jackwayne234/binary-optical-chip/Research/papers/paper_source/main.tex

\documentclass{article}
\usepackage{graphicx} % Required for inserting images

\title{Wavelength Ternary Computing}
\author{Christopher Jack Wayne Riner}
\date{January 2026}

\begin{document}

\maketitle

\section{Introduction}

\end{document}
