jackwayne234/binary-optical-chip/docs/SESSION_NOTES_2026-02-02.md

# Session Notes - February 2, 2026

## Summary

Comprehensive session covering GDS chip generation, GitHub organization, and foundry submission preparation for the 81-trit ternary optical computer.

---

## What We Accomplished

### 1. GitHub Repository Cleanup
- Uploaded `ternary_81trit_optimal.gds` to GitHub
- Reorganized root directory:
  - Moved setup guides to `docs/guides/`
  - Moved shell scripts to `bin/`
  - Moved `citations.bib` to `Research/papers/`
- Added `.gitignore` entries for local files (ebay files, CLAUDE.md, etc.)
- Fixed `tools/README.md` URL (Replit → Render.com)
- Updated README with:
  - Table of contents
  - Recent activity section (collapsible)

### 2. Foundry Submission Documents
- Created `Phase3_Chip_Simulation/DESIGN_SUMMARY.md` - complete design datasheet
- Created `Phase3_Chip_Simulation/foundry_inquiry_email.txt` - template email

**Foundries to contact:**
- Applied Nanotools (Canada) - info@appliednt.com
- Ligentec (Switzerland) - mpw@ligentec.com
- HyperLight (Boston) - info@hyperlightcorp.com (best for LiNbO3)
- AIM Photonics (US) - info@aimphotonics.com

### 3. Chip Generator Enhancements

**New components added:**
- `kerr_resonator()` - Optical clock/timing (layer 5)
- `y_junction()` - Beam splitter
- `awg_demux()` - Arrayed Waveguide Grating for R/G/B separation (layer 6)
- `optical_frontend()` - Complete input stage
- `ternary_output_stage()` - 3-channel wavelength-discriminating detector
- `generate_complete_alu()` - Full ALU with frontend + output
- `generate_complete_81_trit()` - Full 81-trit chip

**Menu options:**
```
1-4:  Basic operations (add/sub/mul/div)
5:    Single ALU (configurable)
6:    N-trit processor
7:    Power-of-3 processor
8:    81-trit processor (basic)
9:    Custom components (a-k)
10:   Complete ALU (frontend + ALU + output)
11:   FULL 81-TRIT CHIP [RECOMMENDED]
```

**Labels:**
- Now on dedicated layer **100/0** (toggle in KLayout)
- Shortened to standard naming: SEL_1550, DET_R, A, B, Q, MIX, etc.

### 4. Architecture Clarification

**Signal flow:**
```
CW Laser → Kerr Clock → Y-Junction → AWG (demux) → Selectors → Combiner →
                                                                    ↓
                                                              SFG Mixer
                                                                    ↓
                                                           Splitter → 3 Photodetectors
                                                                    ↓
                                                           DET_R, DET_G, DET_B (to GPIO)
```

**Interface to binary computer:**
- 6 GPIO outputs: V_red_A, V_grn_A, V_blu_A, V_red_B, V_grn_B, V_blu_B
- 3 GPIO inputs: Detect_R, Detect_G, Detect_B
- RGB lasers always on; resonators gate which colors pass
- Computer sets voltages, physics does the math, read output colors

### 5. GDS Files Generated

| File | Description |
|---|---|
| `ternary_81trit_optimal.gds` | Basic 81-trit (option 8) |
| `ternary_complete_alu.gds` | Single complete ALU (option 10) |
| `ternary_81trit_full.gds` | Full 81-trit with frontend (option 11) |
| `optical_frontend.gds` | Frontend only (option 9→k) |

### 6. KLayout Integration
- Created toggle labels macro: `~/.klayout/macros/toggle_labels.lym`
- Keyboard shortcut: **L** (or Tools → Toggle GDS Labels)
- Labels on layer 100/0 for easy visibility toggle

---

## GDS Layers

| Layer | Purpose |
|---|---|
| 1/0 | Waveguide core |
| 2/0 | SFG mixer region (χ²) |
| 3/0 | Photodetector region |
| 4/0 | DFG divider region |
| 5/0 | Kerr nonlinear region |
| 6/0 | AWG body |
| 100/0 | Labels (toggle in KLayout) |

---

## Next Steps

1. **Generate final GDS** - Run option 11 for full 81-trit chip
2. **Convert design summary to PDF**
3. **Send inquiry emails** to foundries
4. **Wait for PDK** from chosen foundry
5. **Regenerate GDS** with foundry-specific layers
6. **Submit for MPW run**

---

## Commands Reference

```bash
# Run chip generator
./launch_chip_generator.sh

# Or manually:
cd /home/jackwayne/Desktop/Optical_computing
source bin/activate_env.sh
python3 Research/programs/ternary_chip_generator.py

# Open GDS in KLayout
klayout Research/data/ternary_81trit_full.gds
```

---

*Session with Claude Code - Opus 4.5*
