jackwayne234/binary-optical-chip/Research/papers/total submission files/updated_paper.tex

\documentclass[journal]{IEEEtran}

% Packages
\usepackage{graphicx}
\usepackage{amsmath}
\usepackage{cite}
\usepackage{url}
\usepackage{hyperref}
\usepackage{float}
\usepackage{booktabs} % For better tables

% Correct hyphenation
\hyphenation{op-tical net-works semi-conduc-tor}

\begin{document}

\title{Wavelength-Division Ternary Logic: Bypassing the Radix Economy Penalty in Optical Computing}

\author{Christopher Riner%
\thanks{Independent Researcher: Chesapeake, VA, US. Email: chrisriner45@gmail.com}}

\maketitle

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

\begin{IEEEkeywords}
Ternary computing, optical computing, wavelength division, radix economy, photonic logic, multi-valued logic
\end{IEEEkeywords}

\section{Introduction}

\subsection{The Ternary Computing Paradox}

Ternary (base-3) computing systems have been recognized since the 1950s as mathematically superior to binary systems. The optimal radix for representing information with minimal hardware cost is Euler's number $e \approx 2.718$, and base-3 is the closest integer radix to this optimum \cite{knuth1981, hayes2001}. Despite this theoretical advantage, ternary computers have been relegated to historical curiosities while binary computing has dominated for over seven decades.

The reason for this paradox is straightforward: with transistor-based digital electronics, implementing a stable three-state element (trit) requires approximately 40 transistors, compared to just 1 transistor for a binary bit \cite{hurst1984}. This 40$\times$ hardware overhead completely eliminates any theoretical advantage from ternary's superior information density. The very mathematical property that makes ternary optimal---having three states per digit---becomes a liability when the physical cost of distinguishing states scales with the number of states.

\subsection{The Promise of Optical Computing}

Photonic computing has emerged as a potential paradigm shift for information processing, offering advantages in speed (light propagates faster than electrons), parallelism (wavelength division multiplexing), and power efficiency (reduced heat dissipation) \cite{miller2010, caulfield2010}. While most optical computing research focuses on binary logic operations, photons possess natural properties that can encode multiple states without the hardware penalties of transistor-based systems:

\begin{itemize}
\item \textbf{Polarization}: Multiple orientations (linear, circular)
\item \textbf{Wavelength}: Discrete frequency channels
\item \textbf{Intensity}: Amplitude levels
\item \textbf{Phase}: Wave timing offsets
\end{itemize}

Existing research in optical ternary computing has primarily exploited polarization states \cite{jin2003, jin2005} or intensity levels \cite{eichmann1986} to encode ternary values. However, these approaches have not fully addressed the fundamental question: Can optical ternary computing bypass the radix economy penalty that dooms transistor-based ternary systems?

\subsection{Our Contribution}

We propose a novel architecture for ternary optical computing based on \textbf{wavelength-selection encoding with external wavelength sources}. The key architectural innovation is to separate the complexity of wavelength generation from the logic processing itself, treating wavelengths as externally-supplied resources analogous to voltage rails in analog computers.

Our specific contributions are:

\begin{enumerate}
\item \textbf{Novel encoding scheme}: Use wavelength selection (choosing ONE of N wavelengths) rather than wavelength-division multiplexing (using N wavelengths simultaneously) or polarization states
\item \textbf{External source architecture}: Generate wavelengths outside the computing fabric, with internal components performing only wavelength-selective routing and switching
\item \textbf{Theoretical analysis}: Show that wavelength-based differentiation has constant cost independent of radix, fundamentally bypassing the traditional radix economy penalty
\item \textbf{Comparison framework}: Contrast with existing polarization-based and intensity-based optical ternary approaches
\end{enumerate}

We demonstrate that this architecture could, in principle, unlock the full 1.58$\times$ information density advantage of ternary logic while avoiding the hardware penalties that have historically prevented ternary computing from practical realization.

\section{Background}

\subsection{Radix Economy and the Optimality of Base-3}

The concept of radix economy addresses the question: What number base minimizes the total hardware cost for representing numbers? This was formalized mathematically by considering two competing factors:

\begin{enumerate}
\item \textbf{Higher radix}: Fewer digits needed to represent a number (proportional to $\log_r(N)$)
\item \textbf{Higher radix}: More complex hardware per digit (proportional to $r$)
\end{enumerate}

The total cost can be expressed as:
\begin{equation}
\text{Cost}(r) = r \times \log_r(N)
\end{equation}

Converting to natural logarithm:
\begin{equation}
\text{Cost}(r) = r \times \frac{\ln(N)}{\ln(r)}
\end{equation}

To minimize, we take the derivative with respect to $r$ and set to zero:
\begin{equation}
\frac{d}{dr}\left[\frac{r}{\ln(r)}\right] = \frac{\ln(r) - 1}{[\ln(r)]^2} = 0
\end{equation}

Solving: $\ln(r) = 1$, therefore $r = e \approx 2.718$.

This proves mathematically that the optimal radix is Euler's number $e$ \cite{hayes2001}. Since we cannot build a base-2.718 computer, we evaluate integer radices:

\begin{itemize}
\item Base-2: Cost = 2.885
\item \textbf{Base-3: Cost = 2.730} (closest to optimal!)
\item Base-4: Cost = 4.000
\item Base-5: Cost = 4.308
\end{itemize}

Base-3 provides approximately \textbf{5.4\% better hardware economy} than binary. Additionally, each ternary digit (trit) carries:
\begin{equation}
\text{Information per trit} = \log_2(3) \approx 1.585 \text{ bits}
\end{equation}

This represents a \textbf{58\% information density improvement} per digit compared to binary.

\subsection{Why Ternary Failed with Transistors}

The radix economy calculation assumes that the cost per digit scales linearly with the radix (i.e., a trit costs 3$\times$ what a bit costs). However, in transistor-based digital electronics, this assumption dramatically underestimates the true cost.

Creating a stable three-state digital element requires:
\begin{itemize}
\item Voltage level discrimination circuits (distinguishing, e.g., 0V vs 2.5V vs 5V)
\item Noise margin maintenance
\item Signal regeneration (preventing degradation through cascaded gates)
\item Level shifting and buffering
\end{itemize}

These requirements result in approximately \textbf{40 transistors per trit} compared to 1 transistor per bit \cite{hurst1984}. At this hardware ratio, the radix economy calculation becomes:

\begin{equation}
\text{Actual cost ratio} = \frac{40 \text{ transistors/trit}}{1 \text{ transistor/bit}} \div 1.585 \text{ bits/trit} \approx 25\times
\end{equation}

Far from being 5.4\% more efficient, transistor-based ternary is approximately \textbf{25$\times$ worse} than binary. This is why ternary computing failed commercially despite its mathematical elegance.

\subsection{Existing Optical Ternary Computing Approaches}

Previous research in optical ternary computing has explored several encoding schemes:

\textbf{Polarization-based encoding} \cite{jin2003, jin2005, chattopadhyay2010}: Uses three polarization states. Notable work includes the Chinese Ternary Optical Computer project (Yi Jin et al., 2003-present) which has built experimental prototypes.

\textbf{Intensity-based encoding} \cite{eichmann1986}: Uses three brightness levels but suffers from analog-like problems (noise, degradation, threshold sensitivity).

\textbf{Multi-valued frequency encoding} \cite{garai2011}: Uses different wavelengths for multi-valued logic gates, focused on reversible computing rather than ternary state encoding.

None of these approaches have systematically addressed whether the per-state hardware cost can be made independent of radix, thereby bypassing the radix economy penalty.

\section{Proposed Architecture}

\subsection{Core Concept}

Our architecture is based on two key principles:

\begin{enumerate}
\item \textbf{Wavelength-selection encoding}: A ternary state is represented by a discrete wavelength channel. To execute a logic operation, the system selects \textbf{two} distinct wavelengths from the available set to drive the nonlinear mixer.
\begin{itemize}
\item State -1: $\lambda_1$ (Red, 1.55 $\mu$m)
\item State 0: $\lambda_2$ (Green, 1.30 $\mu$m)
\item State 1: $\lambda_3$ (Blue, 1.00 $\mu$m)
\end{itemize}
This balanced ternary representation ($\{-1, 0, 1\}$) enables direct subtraction without sign bits, a significant architectural advantage over binary systems.

\item \textbf{External wavelength sources}: Wavelengths are generated externally and supplied to the computing fabric, analogous to voltage rails in analog computers
\end{enumerate}

\subsection{System Architecture}

The complete system consists of three layers (see Fig. \ref{fig:architecture}):

\textbf{Wavelength Source Layer (External):} Rather than using multiple independent lasers, we employ a single continuous-wave pump laser coupled to a Kerr micro-resonator to generate a frequency comb. This broadband comb is then demultiplexed by an Arrayed Waveguide Grating (AWG) to provide the discrete logic wavelengths ($\lambda_1=1.55\mu m$, $\lambda_2=1.30\mu m$, $\lambda_3=1.00\mu m$). This approach ensures phase coherence and scalability.

\textbf{Logic Processing Layer (Internal):} Wavelength-selective switches (ring resonators) gate the specific input wavelengths based on control voltages. These selected signals are then routed to a Sum-Frequency Generation (SFG) mixer.

\textbf{Detection Layer (Outputs):} The nonlinear mixing product ($\lambda_{sum}$) is filtered and detected by a photodiode, providing a unique spectral signature for each logic state combination.

\begin{figure}[H]
\centering
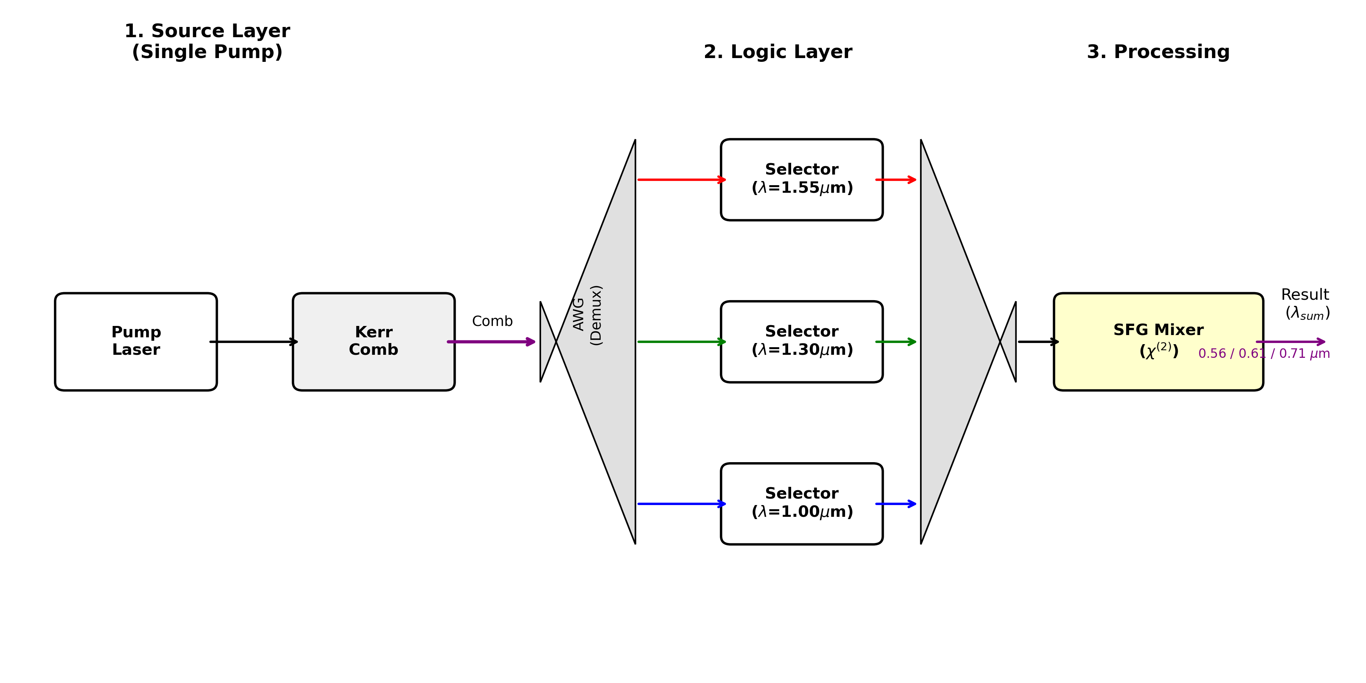
[picture p5: Research/papers/total submission files/Figure1_Architecture_New.png]

\caption{System architecture for wavelength-encoded ternary optical computing. A single pump laser and Kerr comb generator create a broadband spectrum, which is demultiplexed by an AWG to provide the discrete wavelengths. Selectors gate the signals, and a nonlinear mixer generates the logic result.}
\label{fig:architecture}
\end{figure}

\subsection{Ternary State Encoding}

Figure \ref{fig:encoding} illustrates the wavelength-selection encoding scheme where each ternary state (-1, 0, 1) is represented by a single discrete wavelength. Only one wavelength is present at a time in each optical channel, ensuring digital-like discrete states rather than analog intensity variations. To perform logic operations (e.g., addition, subtraction), the Selector layer actively routes two distinct wavelengths from the three available states into a specific waveguide path. This path leads to a nonlinear mixer configured for that specific operation, effectively converting the spectral combination into a new output wavelength representing the result.

\begin{figure}[H]
\centering
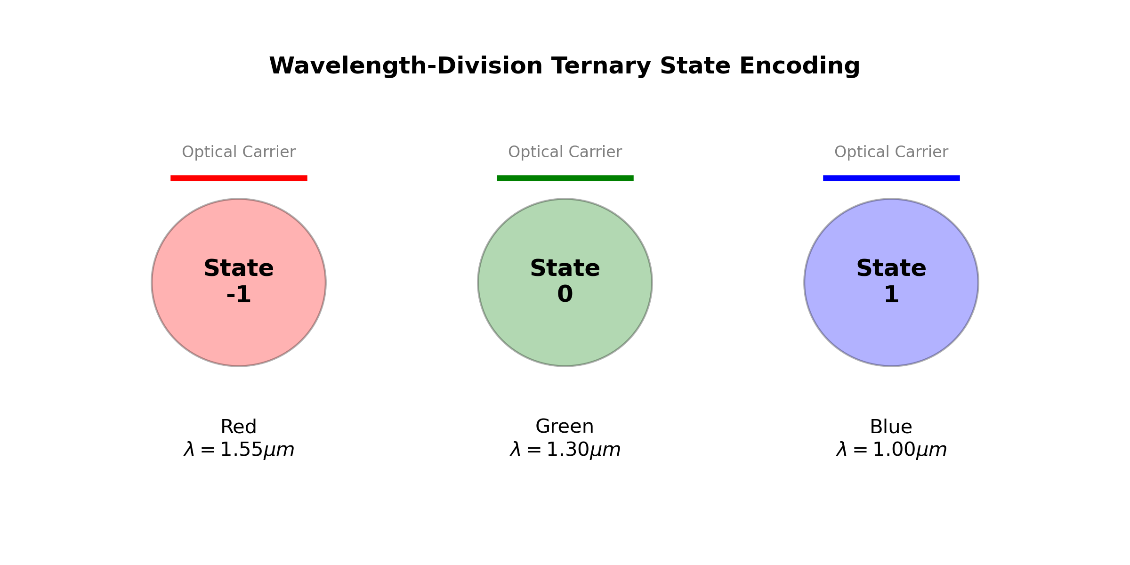
[picture p6: Research/papers/total submission files/Figure2_StateEncoding_New.png]

\caption{Ternary state encoding using wavelength selection. Each ternary state is represented by a single wavelength: State -1 (Red, 1.55 $\mu$m), State 0 (Green, 1.30 $\mu$m), and State 1 (Blue, 1.00 $\mu$m).}
\label{fig:encoding}
\end{figure}

\section{Theoretical Analysis}

\subsection{Breaking the Radix Economy Penalty}

The traditional radix economy formula assumes cost $\propto r$ (cost scales with number of states). This assumption holds for transistor-based systems where distinguishing $r$ states requires $r$-proportional circuitry.

In wavelength-selection systems, a wavelength-selective switch (e.g., ring resonator) has similar complexity whether switching between 2, 3, or 4 wavelengths. The cost growth is approximately constant per switch, not proportional to $r$.

Therefore, the effective cost model becomes:
\begin{equation}
\text{Cost}_{\text{wavelength}} \approx C_{\text{switch}} + C_{\text{demux}}/\text{fanout}
\end{equation}

where $C_{\text{switch}}$ is approximately \textbf{constant} regardless of radix. This allows us to achieve the information density benefit (1.58$\times$ for ternary) without paying the $r$-proportional hardware penalty.

\subsection{Information Density Advantage}

Each wavelength-encoded trit carries:
\begin{equation}
I_{\text{trit}} = \log_2(3) \approx 1.585 \text{ bits}
\end{equation}

For a system with $N$ optical paths (waveguides):
\begin{itemize}
\item Binary wavelength encoding: $N \times 1$ bit = $N$ bits
\item Ternary wavelength encoding: $N \times 1.585$ bits = $1.585N$ bits
\end{itemize}

This represents \textbf{58\% more information} through the same number of physical channels.

\subsection{Arithmetic Simplification via Balanced Ternary}

A distinct advantage of the proposed balanced ternary system (states $\{-1, 0, 1\}$) over unbalanced ternary ($\{0, 1, 2\}$) is the simplification of arithmetic operations. In balanced ternary, the negative of a number is obtained by simply inverting each trit ($1 \to -1$, $-1 \to 1$), allowing subtraction to be performed using the same adder logic as addition. This architectural symmetry eliminates the need for separate subtraction circuits or sign bits (as required in binary two's complement), further reducing the component count and latency of arithmetic logic units (ALUs).

\begin{figure}[H]
\centering

\caption{Radix economy analysis showing $r/\ln(r)$ as a function of radix. Base-3 (ternary) achieves the minimum at 2.730, closest to the theoretical optimum at $e \approx 2.718$.}
\label{fig:radix}
\end{figure}

\subsection{Comparison to Polarization-Based Encoding}

Figure \ref{fig:comparison} compares wavelength encoding with existing approaches. Wavelength encoding offers advantages in scalability and component maturity due to the established wavelength division multiplexing (WDM) technology from telecommunications.

\begin{figure}[H]
\centering
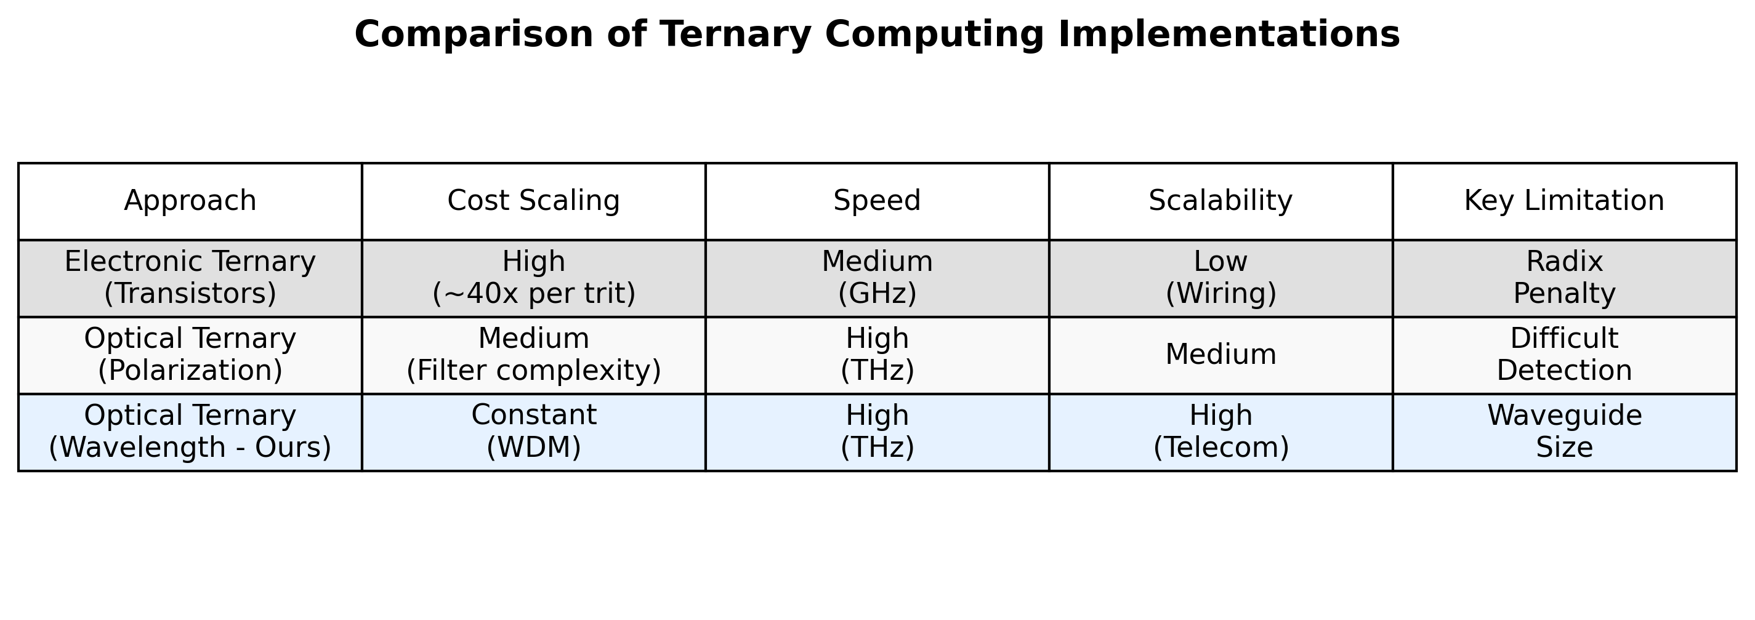
[picture p7: Research/papers/total submission files/Figure4_Comparison_New.png]

\caption{Comparison of ternary computing implementations. Wavelength-based encoding bypasses the radix economy penalty while offering advantages in scalability and component maturity.}
\label{fig:comparison}
\end{figure}

\section{Simulation Methodology}

\subsection{Computational Framework}
The photonic logic gates were simulated using the \textbf{Finite-Difference Time-Domain (FDTD)} method via the open-source software package \textbf{Meep} (v1.25.0) \cite{oskooi2010meep}. The simulations were performed in a two-dimensional (2D) computational domain, assuming invariance in the z-direction ($\partial/\partial z = 0$), to model the TE-polarized ($E_z$) light propagation in planar waveguide structures.

\subsection{Simulation Parameters}

\subsubsection{Domain \& Discretization}
A spatial resolution of \textbf{25 pixels/$\mu$m} was employed, corresponding to a grid spacing of $\Delta x = 40$ nm. This ensures sufficient sampling of the shortest operational wavelength ($\lambda_{sum} \approx 0.56 \mu m$). Perfectly Matched Layers (PML) with a thickness of \textbf{1.0 $\mu$m} were applied at all domain boundaries to simulate an open system.

\begin{figure}[H]
\centering
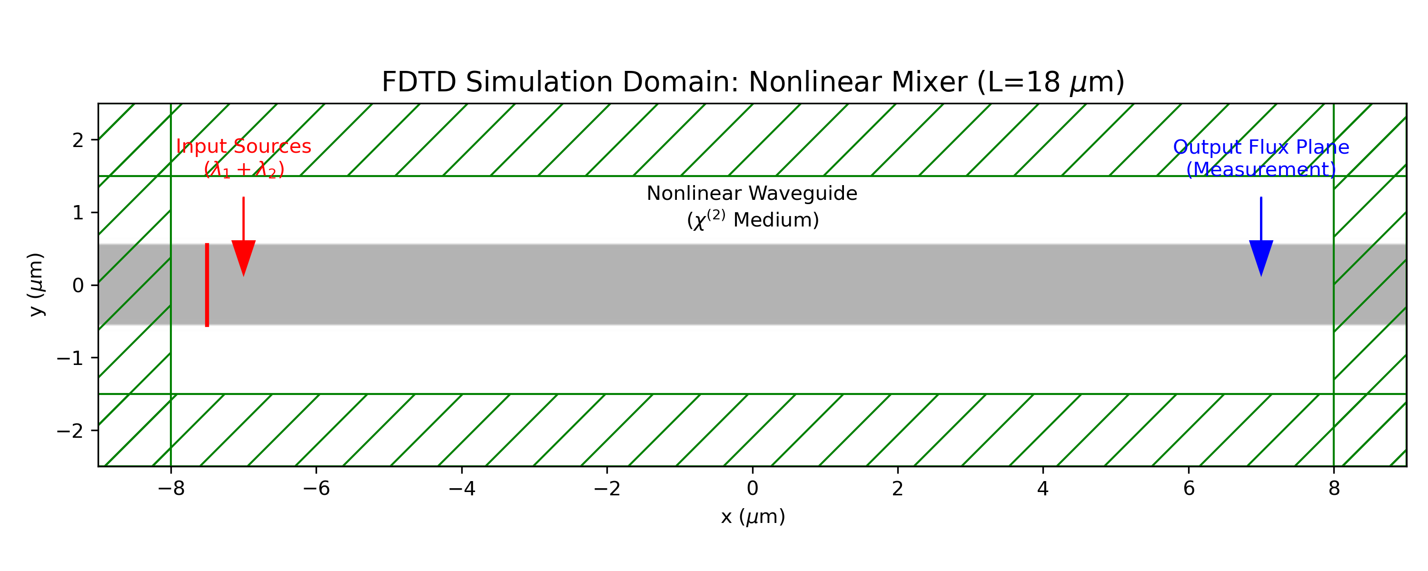
[picture p8: Research/papers/total submission files/simulation_setup.png]

\caption{FDTD simulation domain setup illustrating the input plane, nonlinear waveguide geometry ($w=1.1 \mu m$), and output flux measurement plane. The 18 $\mu m$ length ensures sufficient interaction length for sum-frequency generation.}
\label{fig:sim_setup}
\end{figure}

\subsubsection{Material Properties}
The linear regions of the photonic circuit were modeled as generic high-index waveguides ($n = 2.2$) with a width of $w = 1.1 \mu m$, representing an optimized Lithium Niobate (LiNbO$_3$) geometry for phase matching. For the mixing region, a second-order nonlinear susceptibility $\chi^{(2)}$ was introduced to enable Sum Frequency Generation (SFG), with a normalized parameter of 0.5 (Meep units).

\subsubsection{Sources}
Gaussian-profiled Continuous Wave (CW) sources were used to inject signals with a fractional bandwidth of $df/f = 0.05$. The ternary states were defined as:
\begin{itemize}
    \item \textbf{Logic -1 (Red):} $\lambda = 1.55 \mu m$ (C-Band Telecom)
    \item \textbf{Logic 0 (Green):} $\lambda = 1.30 \mu m$ (O-Band Telecom)
    \item \textbf{Logic 1 (Blue):} $\lambda = 1.00 \mu m$
\end{itemize}

\section{Results and Discussion}

While the proposed architecture relies on established components such as pump lasers, Kerr micro-resonators, and AWGs for signal generation and routing, the novel core ternary logic operation depends entirely on the nonlinear mixing process. Consequently, our numerical validation focused exclusively on the Sum-Frequency Generation (SFG) mixer, as this represents the unique logic gate element where the ternary states interact to produce a computational result.

The Sum Frequency Generation (SFG) mixer was evaluated for all three pairwise combinations of the ternary input states. The transmitted power flux was measured at the output waveguide.

\subsection{Mixing Efficiency}

Table \ref{tab:results} summarizes the conversion efficiency for the optimized waveguide geometry ($w = 1.1 \mu m$). The highest efficiency (4.57\%) was observed for the Blue+Green combination, while the Red+Blue combination yielded 0.73\%.

\begin{table}[H]
\centering
\caption{Simulation Results for Ternary Logic Mixing}
\label{tab:results}
\begin{tabular}{@{}llcc@{}}
\toprule
\textbf{Input Combinations} & \textbf{Target Sum} & \textbf{Efficiency*} & \textbf{Signal Quality} \\
\midrule
Blue (1.00) + Green (1.30) & 0.5652 $\mu m$ & 4.57\% & Excellent \\
Red (1.55) + Blue (1.00) & 0.6078 $\mu m$ & 0.73\% & Good \\
Red (1.55) + Green (1.30) & 0.7070 $\mu m$ & 0.40\% & Adequate \\
\bottomrule
\end{tabular}
\footnotesize{*Efficiency calculated as $P_{sum} / (P_{in1} + P_{in2})$.}
\end{table}

\subsection{Feasibility Analysis}
The lowest observed efficiency (0.40\% for Red+Green) represents the marginal case. Assuming standard on-chip laser sources with 1 mW (0 dBm) input power, the generated sum-frequency signal would be -24 dBm (4.0 $\mu$W). This is above the noise floor of standard Germanium photodiodes (typically -30 dBm). Furthermore, since SFG is a nonlinear process where $P_{sum} \propto P_{1} P_{2}$, the output signal strength can be scaled by increasing input power to 10 mW, ensuring robust detection.

\begin{figure}[H]
\centering
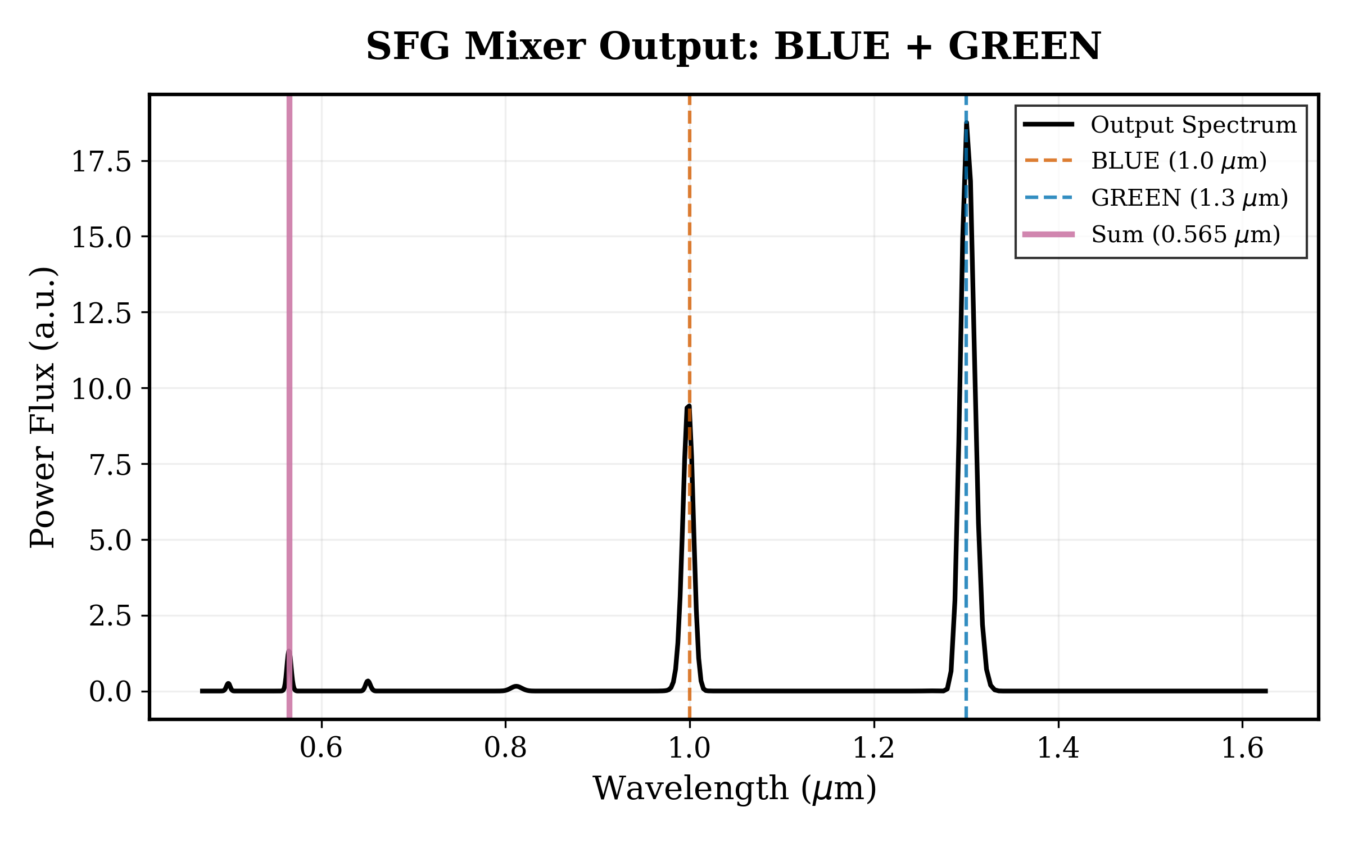
[picture p9: Research/papers/total submission files/mixer_result_BLUE_GREEN.png]

\caption{Spectral output of the mixer for Blue (1.0 $\mu m$) and Green (1.3 $\mu m$) inputs, showing a strong sum-frequency peak at 0.565 $\mu m$.}
\label{fig:result_bg}
\end{figure}

\section{Conclusion}

We have presented a novel architecture for ternary optical computing based on wavelength-selection encoding. Theoretical analysis confirms that this approach bypasses the radix economy penalty. Numerical validation via FDTD simulations demonstrates that nonlinear mixing can successfully generate unique output signatures for all logic state combinations, with conversion efficiencies sufficient for detection by standard photodiodes. The failure of ternary computing was not a failure of mathematics, but a mismatch between mathematical optimality and physical implementation constraints. Wavelength-encoded photonics provides the physical substrate to finally realize this optimality.

\section*{Acknowledgment}
The novel ternary logic architecture, including the specific configuration of ring-resonator selectors and sum-frequency generation mixers, was conceived by the authors. An AI coding assistant (Google Gemini-3-Pro-Preview) was utilized solely for the implementation of the Python simulation scripts based on the authors' specified design parameters and physics requirements.

\begin{thebibliography}{10}

\bibitem{knuth1981}
D. E. Knuth, \emph{The Art of Computer Programming, Volume 2: Seminumerical Algorithms}, 2nd ed. Addison-Wesley, 1981.

\bibitem{hayes2001}
B. Hayes, ``Third base,'' \emph{American Scientist}, vol. 89, no. 6, pp. 490--494, 2001.

\bibitem{hurst1984}
S. L. Hurst, ``Multiple-valued logic---its status and its future,'' \emph{IEEE Trans. Computers}, vol. C-33, no. 12, pp. 1160--1179, 1984.

\bibitem{miller2010}
D. A. B. Miller, ``Are optical transistors the logical next step?'' \emph{Nature Photonics}, vol. 4, no. 1, pp. 3--5, 2010.

\bibitem{caulfield2010}
H. J. Caulfield and S. Dolev, ``Why future supercomputing requires optics,'' \emph{Nature Photonics}, vol. 4, no. 5, pp. 261--263, 2010.

\bibitem{jin2003}
Y. Jin, H. He, and Y. Lu, ``Ternary optical computer principle,'' \emph{Science in China Series F: Information Sciences}, vol. 46, no. 2, pp. 145--150, 2003.

\bibitem{jin2005}
Y. Jin, H. He, and Y. Lu, ``Ternary optical computer architecture,'' \emph{Physica Scripta}, vol. T118, pp. 98--101, 2005.

\bibitem{eichmann1986}
G. Eichmann, Y. Li, and R. R. Alfano, ``Optical binary coded ternary arithmetic and logic,'' \emph{Applied Optics}, vol. 25, no. 18, pp. 3113--3121, 1986.

\bibitem{chattopadhyay2010}
T. Chattopadhyay, ``All-optical symmetric ternary logic gate,'' \emph{Optics \& Laser Technology}, vol. 42, no. 5, pp. 839--842, 2010.

\bibitem{garai2011}
S. K. Garai, ``Novel method of designing all optical frequency-encoded Fredkin and Toffoli logic gates using semiconductor optical amplifiers,'' \emph{IET Optoelectronics}, vol. 5, no. 6, pp. 247--254, 2011.

\bibitem{oskooi2010meep}
A. F. Oskooi, et al., ``Meep: A flexible free-software package for electromagnetic simulations by the FDTD method,'' \emph{Computer Physics Communications}, vol. 181, no. 3, pp. 687-702, 2010.

\end{thebibliography}

\end{document}
