jackwayne234/binary-optical-chip/Research/papers/total submission files/mixer_data_BLUE_GREEN.csv

Frequency (Meep) | Wavelength (um) | Flux (a.u.)
6.153846153846154188e-01 | 1.625000000000000000e+00 | 2.114531186874911402e-10
6.179016309233338333e-01 | 1.618380580264360935e+00 | 2.133539675427316186e-10
6.204186464620521368e-01 | 1.611814870011591294e+00 | 2.199747586257001571e-10
6.229356620007705514e-01 | 1.605302218190813868e+00 | 2.126034032805247608e-10
6.254526775394889659e-01 | 1.598841984231274438e+00 | 1.864630055546871735e-10
6.279696930782072695e-01 | 1.592433537832310897e+00 | 1.917050912007205903e-10
6.304867086169256840e-01 | 1.586076258758350788e+00 | 1.993536322787212391e-10
6.330037241556440986e-01 | 1.579769536638805372e+00 | 1.940160377438790263e-10
6.355207396943624021e-01 | 1.573512770772712566e+00 | 2.391218369924046640e-10
6.380377552330808166e-01 | 1.567305369938008175e+00 | 3.172761871343774208e-10
6.405547707717992312e-01 | 1.561146752205292421e+00 | 4.702781677722418987e-10
6.430717863105175347e-01 | 1.555036344755970967e+00 | 7.722775258701993622e-10
6.455888018492359492e-01 | 1.548973583704646551e+00 | 1.389964143066194193e-09
6.481058173879543638e-01 | 1.542957913925655733e+00 | 2.745068999198991387e-09
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
