jackwayne234/binary-optical-chip/Research/papers/total submission files/mixer_data_RED_BLUE.csv

Frequency (Meep) | Wavelength (um) | Flux (a.u.)
5.161290322580646128e-01 | 1.937499999999999556e+00 | 2.001693435951995215e-14
5.185631967257258168e-01 | 1.928405267311925630e+00 | 4.005100565949355867e-13
5.209973611933869098e-01 | 1.919395518068303774e+00 | 6.055009855848149139e-13
5.234315256610481137e-01 | 1.910469566648832718e+00 | 8.539453493366800631e-13
5.258656901287092067e-01 | 1.901626249385547807e+00 | 1.209222648619264140e-13
5.282998545963704107e-01 | 1.892864424057084216e+00 | 1.169682569547801300e-13
5.307340190640315036e-01 | 1.884182969396866358e+00 | 2.133632663216839636e-12
5.331681835316927076e-01 | 1.875580784614762742e+00 | 4.373518913531590358e-13
5.356023479993539116e-01 | 1.867056788931788391e+00 | 3.490445029522641393e-12
5.380365124670150045e-01 | 1.858609921127436948e+00 | 5.165598711741784951e-12
5.404706769346762085e-01 | 1.850239139099242314e+00 | 1.301296420541534702e-11
5.429048414023373015e-01 | 1.841943419434194151e+00 | 2.323740009390211538e-11
5.453390058699985055e-01 | 1.833721756991625540e+00 | 6.379037522407552179e-11
5.477731703376595984e-01 | 1.825573164497227285e+00 | 1.296605837974325111e-10
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
