jackwayne234/binary-optical-chip/Research/papers/total submission files/mixer_data_RED_GREEN.csv

Frequency (Meep) | Wavelength (um) | Flux (a.u.)
5.161290322580646128e-01 | 1.937499999999999556e+00 | 1.571528116266899811e-01
5.181008877492264686e-01 | 1.930126011449770917e+00 | 1.863109668609688740e-01
5.200727432403883244e-01 | 1.922807939845790903e+00 | 2.025842528575005630e-01
5.220445987315501801e-01 | 1.915545151563243564e+00 | 2.017879745649237833e-01
5.240164542227120359e-01 | 1.908337022514545733e+00 | 1.839061545487996607e-01
5.259883097138738917e-01 | 1.901182937970576026e+00 | 1.531614121471177870e-01
5.279601652050357474e-01 | 1.894082292385913968e+00 | 1.163796860559059565e-01
5.299320206961976032e-01 | 1.887034489227978895e+00 | 8.052619838410568498e-02
5.319038761873594590e-01 | 1.880038940809968695e+00 | 5.061018478675691212e-02
5.338757316785214257e-01 | 1.873095068127501817e+00 | 2.879535081034800825e-02
5.358475871696832815e-01 | 1.866202300698867722e+00 | 1.476567716994767708e-02
5.378194426608451373e-01 | 1.859360076408786533e+00 | 6.783585828941314858e-03
5.397912981520069930e-01 | 1.852567841355598821e+00 | 2.771977420090306846e-03
5.417631536431688488e-01 | 1.845825049701788734e+00 | 1.001716218685555927e-03
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
