jackwayne234/binary-optical-chip/Research/papers/RESULTS_SUMMARY.md

# Photonic Mixer Simulation Log

| Timestamp | Inputs | Target Sum Wvl | Peak Flux (Sum) | Conversion Eff (%) |
|---|---|---|---|---|
| 2026-01-28 13:26:12 | BLUE (1.0) + GREEN (1.3) | 0.5652 um | 3.6810e-01 | 1.71% |
| 2026-01-28 13:39:04 | RED (1.55) + BLUE (1.0) | 0.6078 um | 7.2517e-03 | 0.03% |
| 2026-01-28 13:42:28 | RED (1.55) + GREEN (1.3) | 0.7070 um | 9.2023e-01 | 3.01% |
| 2026-01-28 13:50:39 | RED (1.55) + BLUE (1.0) | 0.6078 um | 2.7652e-01 | 0.73% |
| 2026-01-28 13:51:16 | RED (1.55) + GREEN (1.3) | 0.7070 um | 1.6764e-01 | 0.40% |
| 2026-01-28 13:51:46 | BLUE (1.0) + GREEN (1.3) | 0.5652 um | 1.2875e+00 | 4.57% |
