jackwayne234/binary-optical-chip/Research/programs/ternary_chip_generator.py

# Copyright (c) 2026 Christopher Riner
# Licensed under the MIT License. See LICENSE file for details.
#
# Wavelength-Division Ternary Optical Computer
# High-Level Chip Generator
#
# Automatically generates photonic chip layouts from high-level specifications.
# Specify the logic operation you want, and this generates the full chip.

import gdsfactory as gf
from gdsfactory.routing import route_single
import numpy as np
from typing import List, Dict, Optional, Literal

# Import IOC module for electronic-optical interface
from ioc_module import (
    ioc_module_complete,
    ioc_encoder_unit,
    ioc_decoder_unit,
    tier1_adapter,
    tier2_adapter,
    tier3_adapter
)

# Import Optical Backplane for system interconnect
from optical_backplane import (
    optical_backplane,
    mini_backplane,
    backplane_slot,
    crossbar_switch,
    optical_bus,
    backplane_edfa,
    kerr_clock_hub,
    backplane_central_clock,
    round_table_backplane  # Primary Round Table architecture
)

# Import IOA module for external adapters
from ioa_module import (
    ioa_system_complete,
    electronic_ioa,
    network_ioa,
    sensor_ioa,
    ioa_controller
)

# Import Storage IOA for memory interfaces
from storage_ioa import (
    storage_ioa,
    nvme_controller,
    ddr5_phy,
    hbm_phy
)

# Import OPU Controller (the brain)
from opu_controller import (
    opu_controller,
    command_queue,
    ternary_instruction_decoder,
    ternary_branch_predictor
)

# Activate the generic PDK
gf.gpdk.PDK.activate()

# Default cross-section for routing
XS = gf.cross_section.strip(width=0.5)

# Dedicated layer for labels (toggle visibility in KLayout)
LABEL_LAYER = (100, 0)

# Layer for MZI heaters/electrodes
HEATER_LAYER = (10, 0)

# =============================================================================
# TERNARY ENCODING: Wavelength -> Value
# =============================================================================
# Input wavelengths chosen so that R+B and G+G produce same SFG output (both = 0)
# Green = harmonic mean of Red and Blue: λ_G = 2*λ_R*λ_B/(λ_R+λ_B) = 1.216 μm
TERNARY_ENCODING = {
    'NEG':   {'value': -1, 'wavelength_um': 1.550, 'color': 'red',   'name': 'Red'},
    'ZERO':  {'value':  0, 'wavelength_um': 1.216, 'color': 'green', 'name': 'Green'},
    'POS':   {'value': +1, 'wavelength_um': 1.000, 'color': 'blue',  'name': 'Blue'},
}

# SFG Output wavelengths (verified by simulation)
# These are what the detectors need to sense
OUTPUT_ENCODING = {
    'NEG2':  {'value': -2, 'wavelength_um': 0.775, 'name': 'Overflow-'},  # R+R
    'NEG':   {'value': -1, 'wavelength_um': 0.681, 'name': 'Result-1'},   # R+G
    'ZERO':  {'value':  0, 'wavelength_um': 0.608, 'name': 'Result0'},    # R+B or G+G
    'POS':   {'value': +1, 'wavelength_um': 0.549, 'name': 'Result+1'},   # G+B
    'POS2':  {'value': +2, 'wavelength_um': 0.500, 'name': 'Overflow+'},  # B+B
}

# Material parameters (from your simulations)
MATERIALS = {
    'LiNbO3': {'n_core': 2.2, 'n_clad': 1.0, 'chi2': 0.5},
    'SU8':    {'n_core': 1.57, 'n_clad': 1.0, 'chi2': 0.0},
    'Polymer': {'n_core': 1.50, 'n_clad': 1.0, 'chi2': 0.3},
}

# =============================================================================
# COMPONENT LIBRARY: Ternary Photonic Building Blocks
# =============================================================================

def mzi_switch(
    arm_length: float = 50.0,
    arm_spacing: float = 10.0,
    coupler_length: float = 10.0,
    heater_length: float = 30.0,
    heater_width: float = 2.0,
    name: str = "mzi_switch"
) -> gf.Component:
    """
    Creates a Mach-Zehnder Interferometer (MZI) switch.

    MZI advantages over ring resonators:
    - Better extinction ratio (>30dB vs ~20dB)
    - More tolerant to fabrication variations
    - Broader wavelength bandwidth
    - Simpler tuning (voltage-based phase control)

    Structure:
        Input → 3dB Coupler → Upper Arm (with heater) → 3dB Coupler → Bar Output
                           → Lower Arm              →             → Cross Output

    The control voltage on the heater creates a phase shift via thermo-optic
    effect, switching light between the bar and cross outputs.

    Args:
        arm_length: Length of each MZI arm (um)
        arm_spacing: Vertical spacing between arms (um)
        coupler_length: Length of 3dB MMI couplers (um)
        heater_length: Length of heater/electrode region (um)
        heater_width: Width of heater strip (um)
        name: Component name
    """
    c = gf.Component(name)

    # Input 3dB coupler (MMI-based)
    coupler_in = c << gf.components.mmi1x2()
    coupler_in.dmove((0, 0))

    # Upper arm waveguide
    arm_upper = c << gf.components.straight(length=arm_length, width=0.5)
    arm_upper.dmove((coupler_length + 5, arm_spacing / 2))

    # Lower arm waveguide
    arm_lower = c << gf.components.straight(length=arm_length, width=0.5)
    arm_lower.dmove((coupler_length + 5, -arm_spacing / 2))

    # Route input coupler to arms
    route_single(c, cross_section=XS, port1=coupler_in.ports["o2"], port2=arm_upper.ports["o1"])
    route_single(c, cross_section=XS, port1=coupler_in.ports["o3"], port2=arm_lower.ports["o1"])

    # Output 3dB coupler (2x2 MMI for two outputs)
    coupler_out = c << gf.components.mmi2x2()
    coupler_out.dmove((coupler_length + arm_length + 15, 0))

    # Route arms to output coupler
    route_single(c, cross_section=XS, port1=arm_upper.ports["o2"], port2=coupler_out.ports["o1"])
    route_single(c, cross_section=XS, port1=arm_lower.ports["o2"], port2=coupler_out.ports["o2"])

    # Heater/electrode on upper arm (for thermo-optic phase control)
    heater_x = coupler_length + 5 + (arm_length - heater_length) / 2
    heater_y = arm_spacing / 2 + 1.0  # Offset above waveguide
    c.add_polygon(
        [
            (heater_x, heater_y),
            (heater_x + heater_length, heater_y),
            (heater_x + heater_length, heater_y + heater_width),
            (heater_x, heater_y + heater_width)
        ],
        layer=HEATER_LAYER
    )

    # Contact pads for heater
    pad_size = 5.0
    # Left pad
    c.add_polygon(
        [
            (heater_x - pad_size, heater_y),
            (heater_x, heater_y),
            (heater_x, heater_y + heater_width + pad_size),
            (heater_x - pad_size, heater_y + heater_width + pad_size)
        ],
        layer=HEATER_LAYER
    )
    # Right pad
    c.add_polygon(
        [
            (heater_x + heater_length, heater_y),
            (heater_x + heater_length + pad_size, heater_y),
            (heater_x + heater_length + pad_size, heater_y + heater_width + pad_size),
            (heater_x + heater_length, heater_y + heater_width + pad_size)
        ],
        layer=HEATER_LAYER
    )

    # Labels
    c.add_label("MZI", position=(coupler_length + arm_length / 2, arm_spacing + 5), layer=LABEL_LAYER)
    c.add_label("HTR", position=(heater_x + heater_length / 2, heater_y + heater_width + 2), layer=LABEL_LAYER)

    # Ports
    c.add_port(name="input", port=coupler_in.ports["o1"])
    c.add_port(name="bar", port=coupler_out.ports["o3"])    # Straight-through when heater OFF
    c.add_port(name="cross", port=coupler_out.ports["o4"])  # Cross output when heater ON
    # Alias for compatibility
    c.add_port(name="output", port=coupler_out.ports["o3"])

    return c


def wavelength_selector_mzi(
    wavelength_um: float,
    arm_length: float = 50.0,
    arm_spacing: float = 10.0,
    name: str = "selector_mzi"
) -> gf.Component:
    """
    Creates an MZI-based wavelength selector (gating switch).

    Unlike ring resonators which filter by wavelength, MZI switches gate
    light on/off. For wavelength selection, use with an upstream AWG demux
    that separates wavelengths, then MZI switches gate each channel.

    MZI advantages over ring resonators:
    - Better extinction ratio (>30dB vs ~20dB for rings)
    - More tolerant to fabrication variations (no critical gap)
    - Broader wavelength bandwidth (works across entire channel)
    - Simpler tuning (just voltage, no resonance tracking)

    Args:
        wavelength_um: Target wavelength (for labeling/documentation)
        arm_length: MZI arm length (um)
        arm_spacing: Spacing between MZI arms (um)
        name: Component name

    Note: The wavelength_um parameter is primarily for labeling. The MZI
    itself is broadband and will switch any wavelength. Wavelength
    selectivity comes from the upstream AWG demux.
    """
    c = gf.Component(name)

    # MZI switch core
    mzi = c << mzi_switch(
        arm_length=arm_length,
        arm_spacing=arm_spacing,
        name=f"mzi_core_{name}"
    )

    # Add wavelength label for documentation
    wl_nm = int(wavelength_um * 1000)
    c.add_label(f"MZI_{wl_nm}", position=(0, arm_spacing + 10), layer=LABEL_LAYER)

    # Expose ports
    c.add_port(name="input", port=mzi.ports["input"])
    c.add_port(name="output", port=mzi.ports["output"])
    c.add_port(name="bar", port=mzi.ports["bar"])
    c.add_port(name="cross", port=mzi.ports["cross"])

    return c


def wavelength_selector(
    wavelength_um: float,
    radius: float = 5.0,
    gap: float = 0.15,
    name: str = "selector"
) -> gf.Component:
    """
    Creates a ring resonator wavelength selector.

    This selects a specific wavelength from a multi-wavelength input.
    When voltage is applied, it shifts the resonance (ON/OFF control).

    Args:
        wavelength_um: Target wavelength to select
        radius: Ring radius (larger = sharper filter)
                Note: Simulation optimal is 0.8um for LiNbO3, but generic PDK
                requires min 5.0um. Use foundry PDK for actual values.
        gap: Coupling gap (simulation: 0.15um)
        name: Component name
    """
    c = gf.Component(name)

    # Ring resonator - the core selector element
    ring = c << gf.components.ring_single(radius=radius, gap=gap)

    # Add labels for clarity
    wl_nm = int(wavelength_um * 1000)
    c.add_label(f"SEL_{wl_nm}", position=(0, radius + 2), layer=LABEL_LAYER)

    # Expose ports
    c.add_port(name="input", port=ring.ports["o1"])
    c.add_port(name="output", port=ring.ports["o2"])

    return c


def wavelength_inverter(
    name: str = "inverter"
) -> gf.Component:
    """
    Creates a wavelength inverter for ternary negation.

    Swaps Red (1.55μm, -1) ↔ Blue (1.00μm, +1), Green (0) unchanged.
    This enables subtraction: A - B = A + (-B)

    Implementation: Uses wavelength-selective crossings
    - Red and Blue paths cross over
    - Green path passes straight through
    """
    c = gf.Component(name)

    # Three parallel paths with crossover for Red and Blue
    # Red input (top) -> Blue output (bottom)
    # Green input (middle) -> Green output (middle)
    # Blue input (bottom) -> Red output (top)

    spacing = 5
    length = 30

    # Input waveguides
    wg_top = c << gf.components.straight(length=10, width=0.5)
    wg_top.dmove((0, spacing))

    wg_mid = c << gf.components.straight(length=length, width=0.5)
    wg_mid.dmove((0, 0))

    wg_bot = c << gf.components.straight(length=10, width=0.5)
    wg_bot.dmove((0, -spacing))

    # Crossing region (Red↔Blue swap)
    cross = c << gf.components.crossing()
    cross.dmove((15, 0))
    cross.drotate(45)

    # Output waveguides
    wg_top_out = c << gf.components.straight(length=10, width=0.5)
    wg_top_out.dmove((length - 10, spacing))

    wg_bot_out = c << gf.components.straight(length=10, width=0.5)
    wg_bot_out.dmove((length - 10, -spacing))

    c.add_label("INV", position=(15, spacing + 3), layer=LABEL_LAYER)

    # Ports
    c.add_port(name="input", port=wg_mid.ports["o1"])
    c.add_port(name="output", port=wg_mid.ports["o2"])

    return c


def dfg_divider(
    length: float = 40.0,
    width: float = 0.8,
    name: str = "dfg_divider"
) -> gf.Component:
    """
    Creates a Difference-Frequency Generation divider.

    Uses DFG (χ² nonlinearity) for frequency subtraction.
    Division in ternary is implemented as repeated DFG operations.

    Note: True division requires multiple stages with feedback.
    This is a single-stage approximation.
    """
    c = gf.Component(name)

    # Longer waveguide for DFG (needs more interaction length)
    wg = c << gf.components.straight(length=length, width=width)

    # Visual marker for DFG region
    c.add_polygon(
        [(0, -width), (length, -width), (length, -width-0.5), (0, -width-0.5)],
        layer=(4, 0)  # Different layer for DFG marker
    )
    c.add_label("DFG", position=(length/2, -width - 1), layer=LABEL_LAYER)

    c.add_port(name="input", port=wg.ports["o1"])
    c.add_port(name="output", port=wg.ports["o2"])

    return c


def sfg_mixer(
    length: float = 20.0,
    width: float = 0.8,
    name: str = "sfg_mixer"
) -> gf.Component:
    """
    Creates a Sum-Frequency Generation mixer for ADDITION.

    Mixes two wavelengths via χ² nonlinearity to produce sum frequency.
    Output wavelength: λ_out = 1/(1/λ1 + 1/λ2)
    This effectively computes A + B in ternary.

    Args:
        length: Mixer waveguide length (longer = more mixing)
        width: Waveguide width
        name: Component name
    """
    c = gf.Component(name)

    # Straight waveguide with nonlinear material
    wg = c << gf.components.straight(length=length, width=width)

    # Add a visual marker for the nonlinear region
    c.add_polygon(
        [(0, -width), (length, -width), (length, -width-0.5), (0, -width-0.5)],
        layer=(2, 0)  # Different layer for χ² region marker
    )
    c.add_label("SFG", position=(length/2, -width - 1), layer=LABEL_LAYER)

    c.add_port(name="input", port=wg.ports["o1"])
    c.add_port(name="output", port=wg.ports["o2"])

    return c


def dfg_mixer(
    length: float = 25.0,
    width: float = 0.8,
    name: str = "dfg_mixer"
) -> gf.Component:
    """
    Creates a Difference-Frequency Generation mixer for SUBTRACTION.

    Uses DFG (χ² nonlinearity) for frequency subtraction.
    Output wavelength: λ_out = 1/(1/λ1 - 1/λ2)
    This effectively computes A - B in ternary.

    The DFG process requires slightly longer interaction length than SFG
    for efficient conversion.

    Args:
        length: Mixer waveguide length (longer = more mixing)
        width: Waveguide width
        name: Component name
    """
    c = gf.Component(name)

    # Longer waveguide for DFG (needs more interaction length)
    wg = c << gf.components.straight(length=length, width=width)

    # Visual marker for DFG region (layer 4)
    c.add_polygon(
        [(0, -width), (length, -width), (length, -width-0.5), (0, -width-0.5)],
        layer=(4, 0)  # Different layer for DFG marker
    )
    c.add_label("DFG", position=(length/2, -width - 1), layer=LABEL_LAYER)

    c.add_port(name="input", port=wg.ports["o1"])
    c.add_port(name="output", port=wg.ports["o2"])

    return c


def mul_mixer(
    length: float = 30.0,
    width: float = 0.8,
    name: str = "mul_mixer"
) -> gf.Component:
    """
    Creates a multiplication mixer using Kerr effect (χ³ nonlinearity).

    Implements balanced ternary multiplication:
      (-1) × (-1) = +1
      (-1) × ( 0) =  0
      (-1) × (+1) = -1
      ( 0) × (-1) =  0
      ( 0) × ( 0) =  0
      ( 0) × (+1) =  0
      (+1) × (-1) = -1
      (+1) × ( 0) =  0
      (+1) × (+1) = +1

    The Kerr effect (third-order nonlinearity) enables intensity-dependent
    phase modulation. Combined with wavelength encoding:
      - Same sign inputs (R+R or B+B) -> cross-phase modulation -> same sign output
      - Opposite sign inputs (R+B) -> destructive interference -> opposite sign output
      - Zero input (G) -> no phase shift -> zero output

    Requires longer interaction length for χ³ compared to χ² processes.

    Args:
        length: Mixer waveguide length (χ³ needs longer length)
        width: Waveguide width
        name: Component name
    """
    c = gf.Component(name)

    # Longer waveguide for Kerr effect (χ³ needs more interaction)
    wg = c << gf.components.straight(length=length, width=width)

    # Visual marker for Kerr/χ³ region (layer 7)
    c.add_polygon(
        [(0, -width), (length, -width), (length, -width-0.5), (0, -width-0.5)],
        layer=(7, 0)  # Different layer for χ³ region marker
    )
    c.add_label("MUL", position=(length/2, -width - 1), layer=LABEL_LAYER)

    c.add_port(name="input", port=wg.ports["o1"])
    c.add_port(name="output", port=wg.ports["o2"])

    return c


def universal_alu_mixer(
    name: str = "universal_alu",
    uid: str = ""
) -> gf.Component:
    """
    Creates a universal ALU mixer with ALL FOUR operations using log-domain.

    Log-domain insight:
      - Multiply = add in log domain: ln(A) + ln(B) = ln(A×B)
      - Divide = subtract in log domain: ln(A) - ln(B) = ln(A/B)

    So we only need TWO mixers (SFG and DFG) plus log/exp converters!

    Architecture:
                         ┌──────────────────────────────────────┐
        Linear path:     │  Input ─────────────────→ Mixer ─────────────────→ Output
                         │                            │                         │
        Log path:        │  Input ──→ LOG ──→ Mixer ──┼──→ EXP ──→ Output       │
                         └──────────────────────────────────────┘

    Operations:
      - ctrl_linear + ctrl_sfg → Addition (A + B)
      - ctrl_linear + ctrl_dfg → Subtraction (A - B)
      - ctrl_log + ctrl_sfg → Multiplication (A × B)
      - ctrl_log + ctrl_dfg → Division (A ÷ B)

    Args:
        name: Component name
        uid: Unique identifier for sub-component names
    """
    import uuid as uuid_mod
    if not uid:
        uid = str(uuid_mod.uuid4())[:8]

    c = gf.Component(name)

    # === INPUT STAGE ===
    input_split = c << gf.components.mmi1x2()
    input_split.dmove((0, 0))

    # === LINEAR PATH (top) - bypass log converter ===
    mzi_linear = c << mzi_switch(arm_length=25, name=f"mzi_lin_{uid}")
    mzi_linear.dmove((40, 25))
    route_single(c, cross_section=XS, port1=input_split.ports["o2"], port2=mzi_linear.ports["input"])

    # === LOG PATH (bottom) - through log converter ===
    log_conv = c << optical_log_converter(length=35, name=f"log_{uid}")
    log_conv.dmove((25, -25))
    route_single(c, cross_section=XS, port1=input_split.ports["o3"], port2=log_conv.ports["input"])

    mzi_log = c << mzi_switch(arm_length=25, name=f"mzi_log_{uid}")
    mzi_log.dmove((80, -25))
    route_single(c, cross_section=XS, port1=log_conv.ports["output"], port2=mzi_log.ports["input"])

    # === COMBINE BEFORE MIXER ===
    pre_mix = c << gf.components.mmi2x2()
    pre_mix.dmove((140, 0))
    route_single(c, cross_section=XS, port1=mzi_linear.ports["bar"], port2=pre_mix.ports["o1"])
    route_single(c, cross_section=XS, port1=mzi_log.ports["bar"], port2=pre_mix.ports["o2"])

    # === MIXER SELECTION ===
    mixer_split = c << gf.components.mmi1x2()
    mixer_split.dmove((170, 0))
    route_single(c, cross_section=XS, port1=pre_mix.ports["o3"], port2=mixer_split.ports["o1"])

    # SFG mixer (add in linear, multiply in log)
    mzi_sfg = c << mzi_switch(arm_length=20, name=f"mzi_sfg_{uid}")
    mzi_sfg.dmove((200, 20))
    route_single(c, cross_section=XS, port1=mixer_split.ports["o2"], port2=mzi_sfg.ports["input"])

    mixer_sfg = c << sfg_mixer(length=20, name=f"sfg_{uid}")
    mixer_sfg.dmove((270, 20))
    route_single(c, cross_section=XS, port1=mzi_sfg.ports["bar"], port2=mixer_sfg.ports["input"])

    # DFG mixer (subtract in linear, divide in log)
    mzi_dfg = c << mzi_switch(arm_length=20, name=f"mzi_dfg_{uid}")
    mzi_dfg.dmove((200, -20))
    route_single(c, cross_section=XS, port1=mixer_split.ports["o3"], port2=mzi_dfg.ports["input"])

    mixer_dfg = c << dfg_mixer(length=25, name=f"dfg_{uid}")
    mixer_dfg.dmove((270, -20))
    route_single(c, cross_section=XS, port1=mzi_dfg.ports["bar"], port2=mixer_dfg.ports["input"])

    # === COMBINE MIXER OUTPUTS ===
    post_mix = c << gf.components.mmi2x2()
    post_mix.dmove((310, 0))
    route_single(c, cross_section=XS, port1=mixer_sfg.ports["output"], port2=post_mix.ports["o1"])
    route_single(c, cross_section=XS, port1=mixer_dfg.ports["output"], port2=post_mix.ports["o2"])

    # === OUTPUT STAGE ===
    output_split = c << gf.components.mmi1x2()
    output_split.dmove((340, 0))
    route_single(c, cross_section=XS, port1=post_mix.ports["o3"], port2=output_split.ports["o1"])

    # Linear output (bypass exp)
    linear_out = c << gf.components.straight(length=30, width=0.5)
    linear_out.dmove((370, 15))
    route_single(c, cross_section=XS, port1=output_split.ports["o2"], port2=linear_out.ports["o1"])

    # Log output (through exp converter)
    exp_conv = c << optical_exp_converter(length=35, name=f"exp_{uid}")
    exp_conv.dmove((370, -20))
    route_single(c, cross_section=XS, port1=output_split.ports["o3"], port2=exp_conv.ports["input"])

    # Final output combine
    final_combine = c << gf.components.mmi2x2()
    final_combine.dmove((430, 0))
    route_single(c, cross_section=XS, port1=linear_out.ports["o2"], port2=final_combine.ports["o1"])
    route_single(c, cross_section=XS, port1=exp_conv.ports["output"], port2=final_combine.ports["o2"])

    # === CONTROL ELECTRODE PADS ===
    pad_w, pad_h = 18, 12

    # Linear/Log domain select
    c.add_polygon([(45, 48), (45 + pad_w, 48), (45 + pad_w, 48 + pad_h), (45, 48 + pad_h)], layer=HEATER_LAYER)
    c.add_polygon([(85, -50), (85 + pad_w, -50), (85 + pad_w, -50 + pad_h), (85, -50 + pad_h)], layer=HEATER_LAYER)

    # Operation select (SFG/DFG)
    c.add_polygon([(205, 43), (205 + pad_w, 43), (205 + pad_w, 43 + pad_h), (205, 43 + pad_h)], layer=HEATER_LAYER)
    c.add_polygon([(205, -45), (205 + pad_w, -45), (205 + pad_w, -45 + pad_h), (205, -45 + pad_h)], layer=HEATER_LAYER)

    # === LABELS ===
    c.add_label("UNIVERSAL_ALU_v2", position=(220, 60), layer=LABEL_LAYER)
    c.add_label("LOG", position=(40, -40), layer=LABEL_LAYER)
    c.add_label("EXP", position=(385, -35), layer=LABEL_LAYER)
    c.add_label("ADD/MUL", position=(275, 30), layer=LABEL_LAYER)
    c.add_label("SUB/DIV", position=(278, -30), layer=LABEL_LAYER)

    # Operation guide
    c.add_label("LIN+SFG=ADD", position=(100, 55), layer=LABEL_LAYER)
    c.add_label("LIN+DFG=SUB", position=(100, -55), layer=LABEL_LAYER)
    c.add_label("LOG+SFG=MUL", position=(320, 55), layer=LABEL_LAYER)
    c.add_label("LOG+DFG=DIV", position=(320, -55), layer=LABEL_LAYER)

    # === PORTS ===
    c.add_port(name="input", port=input_split.ports["o1"])
    c.add_port(name="output", port=final_combine.ports["o3"])
    c.add_port(name="pump_exp", port=exp_conv.ports["pump"])

    # Control ports
    c.add_port(name="ctrl_linear", center=(54, 54), width=pad_w, orientation=90, layer=HEATER_LAYER)
    c.add_port(name="ctrl_log", center=(94, -44), width=pad_w, orientation=90, layer=HEATER_LAYER)
    c.add_port(name="ctrl_sfg", center=(214, 49), width=pad_w, orientation=90, layer=HEATER_LAYER)
    c.add_port(name="ctrl_dfg", center=(214, -39), width=pad_w, orientation=90, layer=HEATER_LAYER)

    return c


# =============================================================================
# LOG-DOMAIN ARITHMETIC COMPONENTS
# =============================================================================
# Log-domain enables division and simplifies multiplication:
#   - Multiply: ln(A) + ln(B) = ln(A×B) → use SFG (addition)
#   - Divide:   ln(A) - ln(B) = ln(A/B) → use DFG (subtraction)


def optical_log_converter(
    length: float = 50.0,
    name: str = "log_converter"
) -> gf.Component:
    """
    Converts optical signal to log-domain using saturable absorption.

    Physics: At high intensities, saturable absorbers have output proportional
    to log(input) due to absorption saturation:
        I_out ∝ ln(I_in / I_sat + 1)

    Implementation: Doped waveguide (e.g., Er, Yb) operating in saturation.
    The absorption bleaches proportionally to input power.

    For ternary encoding:
        - Input wavelengths: 1.55 μm (R), 1.216 μm (G), 1.00 μm (B)
        - Output: intensity-encoded log values

    Args:
        length: Saturable absorber length (longer = more dynamic range)
        name: Component name
    """
    c = gf.Component(name)

    # Saturable absorber waveguide (doped region)
    wg = c << gf.components.straight(length=length, width=1.0)

    # Visual marker for doped/SA region
    c.add_polygon(
        [(0, -2), (length, -2), (length, 2), (0, 2)],
        layer=(13, 0)  # Log converter layer
    )
    c.add_label("LOG", position=(length/2, 4), layer=LABEL_LAYER)
    c.add_label("ln(I)", position=(length/2, -4), layer=LABEL_LAYER)

    c.add_port(name="input", port=wg.ports["o1"])
    c.add_port(name="output", port=wg.ports["o2"])

    return c


def optical_exp_converter(
    length: float = 50.0,
    name: str = "exp_converter"
) -> gf.Component:
    """
    Converts log-domain signal back to linear using optical gain.

    Physics: Optical amplifiers (SOA, EDWA) have exponential gain:
        I_out = I_in × exp(g × L)

    When the input represents a log value, the exponential gain
    converts it back to linear domain:
        exp(ln(A)) = A

    Implementation: Pumped gain medium (SOA or doped waveguide with pump).

    Args:
        length: Gain medium length
        name: Component name
    """
    c = gf.Component(name)

    # Gain medium waveguide
    wg = c << gf.components.straight(length=length, width=1.0)

    # Pump input for gain
    pump_tap = c << gf.components.mmi1x2()
    pump_tap.dmove((length/2, -15))
    pump_tap.drotate(90)

    # Visual marker for gain region
    c.add_polygon(
        [(0, -2), (length, -2), (length, 2), (0, 2)],
        layer=(14, 0)  # Exp converter layer
    )
    c.add_label("EXP", position=(length/2, 4), layer=LABEL_LAYER)
    c.add_label("e^x", position=(length/2, -4), layer=LABEL_LAYER)

    c.add_port(name="input", port=wg.ports["o1"])
    c.add_port(name="output", port=wg.ports["o2"])
    c.add_port(name="pump", port=pump_tap.ports["o1"])

    return c


def log_domain_processor(
    name: str = "log_domain_proc",
    uid: str = ""
) -> gf.Component:
    """
    Complete log-domain arithmetic unit with bypass for linear operations.

    Architecture:
        Linear path (add/sub):  Input ──────────────────────────→ Mixer ──────────────────────────→ Output
        Log path (mul/div):     Input ──→ LOG ──→ Mixer ──→ EXP ──→ Output

    MZI switches select between linear and log-domain paths.

    Operations:
        - ctrl_linear + SFG → Addition
        - ctrl_linear + DFG → Subtraction
        - ctrl_log + SFG → Multiplication (log-domain add)
        - ctrl_log + DFG → Division (log-domain subtract)

    Args:
        name: Component name
        uid: Unique identifier
    """
    import uuid as uuid_mod
    if not uid:
        uid = str(uuid_mod.uuid4())[:8]

    c = gf.Component(name)

    # === INPUT STAGE ===
    # Split input to linear and log paths
    input_split = c << gf.components.mmi1x2()
    input_split.dmove((0, 0))

    # === LINEAR PATH (top) ===
    linear_wg = c << gf.components.straight(length=120, width=0.5)
    linear_wg.dmove((30, 20))
    route_single(c, cross_section=XS, port1=input_split.ports["o2"], port2=linear_wg.ports["o1"])

    # MZI switch for linear path
    mzi_linear = c << mzi_switch(arm_length=25, name=f"mzi_lin_{uid}")
    mzi_linear.dmove((160, 20))
    route_single(c, cross_section=XS, port1=linear_wg.ports["o2"], port2=mzi_linear.ports["input"])

    # === LOG PATH (bottom) ===
    # Log converter
    log_conv = c << optical_log_converter(length=40, name=f"log_{uid}")
    log_conv.dmove((30, -30))
    route_single(c, cross_section=XS, port1=input_split.ports["o3"], port2=log_conv.ports["input"])

    # MZI switch for log path
    mzi_log = c << mzi_switch(arm_length=25, name=f"mzi_log_{uid}")
    mzi_log.dmove((100, -30))
    route_single(c, cross_section=XS, port1=log_conv.ports["output"], port2=mzi_log.ports["input"])

    # === COMBINE PATHS before mixer ===
    pre_mixer_combine = c << gf.components.mmi2x2()
    pre_mixer_combine.dmove((230, 0))
    route_single(c, cross_section=XS, port1=mzi_linear.ports["bar"], port2=pre_mixer_combine.ports["o1"])
    route_single(c, cross_section=XS, port1=mzi_log.ports["bar"], port2=pre_mixer_combine.ports["o2"])

    # === MIXER STAGE ===
    # SFG for add (linear) or multiply (log)
    mixer_sfg = c << sfg_mixer(length=20, name=f"sfg_{uid}")
    mixer_sfg.dmove((280, 15))

    # DFG for subtract (linear) or divide (log)
    mixer_dfg = c << dfg_mixer(length=25, name=f"dfg_{uid}")
    mixer_dfg.dmove((280, -15))

    # Split to both mixers
    mixer_split = c << gf.components.mmi1x2()
    mixer_split.dmove((255, 0))
    route_single(c, cross_section=XS, port1=pre_mixer_combine.ports["o3"], port2=mixer_split.ports["o1"])
    route_single(c, cross_section=XS, port1=mixer_split.ports["o2"], port2=mixer_sfg.ports["input"])
    route_single(c, cross_section=XS, port1=mixer_split.ports["o3"], port2=mixer_dfg.ports["input"])

    # === OUTPUT STAGE ===
    # Combine mixer outputs
    mixer_combine = c << gf.components.mmi2x2()
    mixer_combine.dmove((320, 0))
    route_single(c, cross_section=XS, port1=mixer_sfg.ports["output"], port2=mixer_combine.ports["o1"])
    route_single(c, cross_section=XS, port1=mixer_dfg.ports["output"], port2=mixer_combine.ports["o2"])

    # === EXP CONVERTER (for log path output) ===
    # Split: linear output bypasses, log output goes through exp
    output_split = c << gf.components.mmi1x2()
    output_split.dmove((350, 0))
    route_single(c, cross_section=XS, port1=mixer_combine.ports["o3"], port2=output_split.ports["o1"])

    # Exp converter for log path
    exp_conv = c << optical_exp_converter(length=40, name=f"exp_{uid}")
    exp_conv.dmove((380, -25))
    route_single(c, cross_section=XS, port1=output_split.ports["o3"], port2=exp_conv.ports["input"])

    # Final output combine
    output_combine = c << gf.components.mmi2x2()
    output_combine.dmove((450, 0))
    route_single(c, cross_section=XS, port1=output_split.ports["o2"], port2=output_combine.ports["o1"])
    route_single(c, cross_section=XS, port1=exp_conv.ports["output"], port2=output_combine.ports["o2"])

    # === CONTROL ELECTRODE PADS ===
    pad_w, pad_h = 15, 12

    # Linear path control
    c.add_polygon([(165, 45), (165 + pad_w, 45), (165 + pad_w, 45 + pad_h), (165, 45 + pad_h)], layer=HEATER_LAYER)
    c.add_label("LIN", position=(172, 60), layer=LABEL_LAYER)

    # Log path control
    c.add_polygon([(105, -55), (105 + pad_w, -55), (105 + pad_w, -55 + pad_h), (105, -55 + pad_h)], layer=HEATER_LAYER)
    c.add_label("LOG", position=(112, -58), layer=LABEL_LAYER)

    # === LABELS ===
    c.add_label("LOG_DOMAIN_PROC", position=(225, 45), layer=LABEL_LAYER)
    c.add_label("+:ADD ×:MUL", position=(290, 25), layer=LABEL_LAYER)
    c.add_label("-:SUB ÷:DIV", position=(290, -25), layer=LABEL_LAYER)

    # === PORTS ===
    c.add_port(name="input", port=input_split.ports["o1"])
    c.add_port(name="output", port=output_combine.ports["o3"])
    c.add_port(name="pump_exp", port=exp_conv.ports["pump"])

    # Control ports
    c.add_port(name="ctrl_linear", center=(172, 51), width=pad_w, orientation=90, layer=HEATER_LAYER)
    c.add_port(name="ctrl_log", center=(112, -49), width=pad_w, orientation=90, layer=HEATER_LAYER)

    return c


# =============================================================================
# OPTICAL CARRY CHAIN COMPONENTS
# =============================================================================
# These components enable fully optical carry propagation between trits,
# eliminating the need for electronic carry logic.

# GDS layer for optical carry components
CARRY_LAYER = (11, 0)

def optical_delay_line(
    delay_ps: float = 20.0,
    name: str = "delay_line"
) -> gf.Component:
    """
    Creates an optical delay line for carry timing synchronization.

    The delay allows the current trit's computation to complete before
    the carry from the previous trit arrives. Using 20ps delay provides
    5ps safety margin over standard SOA recovery times (~15ps).

    Args:
        delay_ps: Desired delay in picoseconds (default: 20ps)
        name: Component name

    Delay calculation:
        Length = delay_ps × c / n_eff
        For LiNbO3 (n_eff ≈ 2.2): 20 ps ≈ 2.73 mm
    """
    c = gf.Component(name)

    # Calculate length: L = t × c / n
    # c = 3e8 m/s = 3e5 μm/ps, n_eff ≈ 2.2
    n_eff = 2.2
    length_um = delay_ps * 300 / n_eff  # μm

    # Use spiral or serpentine to fit long delay in compact area
    # For simplicity, use a serpentine with multiple bends
    n_segments = max(1, int(length_um / 200))  # 200 μm per segment
    segment_length = length_um / n_segments
    spacing = 15  # μm between segments

    if n_segments == 1:
        wg = c << gf.components.straight(length=segment_length)
        c.add_port(name="input", port=wg.ports["o1"])
        c.add_port(name="output", port=wg.ports["o2"])
    else:
        # Create serpentine path
        current_y = 0
        prev_port = None

        for i in range(n_segments):
            seg = c << gf.components.straight(length=segment_length)
            if i % 2 == 0:
                seg.dmove((0, current_y))
            else:
                seg.dmove((0, current_y))
                seg.dmirror()

            if prev_port is not None:
                # Add bend to connect segments
                bend = c << gf.components.bend_euler(radius=5, angle=180)
                bend.dmove((segment_length if i % 2 == 1 else 0, current_y - spacing/2))
                route_single(c, cross_section=XS, port1=prev_port, port2=bend.ports["o1"])
                route_single(c, cross_section=XS, port1=bend.ports["o2"], port2=seg.ports["o1"])

            if i == 0:
                c.add_port(name="input", port=seg.ports["o1"])
            if i == n_segments - 1:
                c.add_port(name="output", port=seg.ports["o2"])

            prev_port = seg.ports["o2"]
            current_y -= spacing

    # Visual marker
    c.add_polygon(
        [(-5, 5), (segment_length + 5, 5), (segment_length + 5, current_y - 5), (-5, current_y - 5)],
        layer=CARRY_LAYER
    )
    c.add_label(f"DLY_{delay_ps:.0f}ps", position=(segment_length/2, 10), layer=LABEL_LAYER)

    return c


def carry_tap(
    name: str = "carry_tap"
) -> gf.Component:
    """
    Extracts carry wavelengths from mixer output.

    Uses add-drop ring resonators to tap:
      - 0.500 μm (carry +1, from B+B = +2)
      - 0.775 μm (borrow -1, from R+R = -2)

    Main signal continues to output stage for detection.
    Carry signals route to wavelength converter.

    Structure:
        Input ──→ Ring_pos (0.500 μm) ──→ Ring_neg (0.775 μm) ──→ thru
                      │ drop                  │ drop
                      ↓                       ↓
                  carry_pos               carry_neg
    """
    c = gf.Component(name)

    # Add-drop ring for carry +1 (0.500 μm)
    # Using ring_double which has add-drop configuration
    ring_pos = c << gf.components.ring_double(radius=5.0, gap=0.15)
    ring_pos.dmove((0, 0))

    # Add-drop ring for borrow -1 (0.775 μm) - cascaded after first ring
    ring_neg = c << gf.components.ring_double(radius=5.0, gap=0.15)
    ring_neg.dmove((40, 0))

    # Route thru port of first ring to input of second
    route_single(c, cross_section=XS, port1=ring_pos.ports["o2"], port2=ring_neg.ports["o1"])

    # Labels
    c.add_label("TAP_500nm", position=(0, 15), layer=LABEL_LAYER)
    c.add_label("TAP_775nm", position=(40, 15), layer=LABEL_LAYER)

    # Ports
    c.add_port(name="input", port=ring_pos.ports["o1"])      # Main input
    c.add_port(name="thru", port=ring_neg.ports["o2"])       # Main signal continues
    c.add_port(name="carry_pos", port=ring_pos.ports["o4"])  # +1 carry (drop port)
    c.add_port(name="carry_neg", port=ring_neg.ports["o4"])  # -1 borrow (drop port)

    c.add_label("CARRY_TAP", position=(20, 25), layer=LABEL_LAYER)

    return c


def wavelength_converter_opa(
    input_wavelength_um: float = 0.500,
    output_wavelength_um: float = 1.000,
    length: float = 30.0,
    name: str = "opa_converter"
) -> gf.Component:
    """
    Converts carry wavelength to input wavelength using Optical Parametric Amplification.

    OPA uses a pump laser to convert signal wavelength:
        ω_signal + ω_pump → ω_idler (conservation of energy)

    For carry conversion:
        0.500 μm (carry +1) + pump → 1.000 μm (Blue = +1)
        0.775 μm (borrow -1) + pump → 1.550 μm (Red = -1)

    The pump wavelength is calculated from:
        1/λ_pump = 1/λ_signal - 1/λ_output

    Args:
        input_wavelength_um: Carry signal wavelength
        output_wavelength_um: Desired output wavelength (input encoding)
        length: Interaction length
        name: Component name
    """
    c = gf.Component(name)

    # Calculate pump wavelength
    pump_wavelength = 1 / (1/input_wavelength_um - 1/output_wavelength_um)

    # OPA crystal/waveguide
    wg = c << gf.components.straight(length=length, width=0.8)

    # Pump input coupler (from side)
    pump_coupler = c << gf.components.mmi1x2()
    pump_coupler.dmove((length/2, -15))
    pump_coupler.drotate(90)

    # Visual marker for OPA region
    c.add_polygon(
        [(0, -2), (length, -2), (length, 2), (0, 2)],
        layer=CARRY_LAYER
    )
    c.add_label(f"OPA", position=(length/2, 5), layer=LABEL_LAYER)
    c.add_label(f"{input_wavelength_um:.3f}→{output_wavelength_um:.3f}",
                position=(length/2, -5), layer=LABEL_LAYER)

    c.add_port(name="input", port=wg.ports["o1"])
    c.add_port(name="output", port=wg.ports["o2"])
    c.add_port(name="pump", port=pump_coupler.ports["o1"])

    return c


def carry_injector(
    name: str = "carry_injector"
) -> gf.Component:
    """
    Injects optical carry signal into next trit's computation.

    Structure:
        carry_in ──→ Combiner ──→ output (to next trit's mixer input)
        signal_in ─┘

    The carry signal (now at input wavelength after OPA conversion)
    is combined with the next trit's A+B signal before the mixer.
    """
    c = gf.Component(name)

    # 2x1 combiner (carry + signal)
    combiner = c << gf.components.mmi2x2()

    c.add_port(name="signal_in", port=combiner.ports["o1"])
    c.add_port(name="carry_in", port=combiner.ports["o2"])
    c.add_port(name="output", port=combiner.ports["o3"])

    c.add_label("CARRY_INJ", position=(10, 10), layer=LABEL_LAYER)

    return c


def optical_carry_unit(
    name: str = "carry_unit",
    uid: str = ""
) -> gf.Component:
    """
    Complete optical carry unit for one trit.

    Handles both carry-out (to next trit) and carry-in (from previous trit).

    Structure:
        carry_in_pos ──→ OPA ──→ ┐
        carry_in_neg ──→ OPA ──→ ├→ Injector ──→ to_mixer
                    signal_in ──→ ┘

        from_mixer ──→ Carry Tap ──→ thru (to detectors)
                              ├──→ carry_out_pos (0.500 μm)
                              └──→ carry_out_neg (0.775 μm)

        carry_out_pos ──→ OPA ──→ Delay ──→ to_next_trit_pos
        carry_out_neg ──→ OPA ──→ Delay ──→ to_next_trit_neg
    """
    import uuid
    if not uid:
        uid = str(uuid.uuid4())[:8]

    c = gf.Component(name)

    # === CARRY INPUT (from previous trit) ===

    # OPA converters for incoming carry
    opa_in_pos = c << wavelength_converter_opa(
        input_wavelength_um=0.500,
        output_wavelength_um=1.000,  # Blue = +1
        name=f"opa_in_pos_{uid}"
    )
    opa_in_pos.dmove((0, 30))

    opa_in_neg = c << wavelength_converter_opa(
        input_wavelength_um=0.775,
        output_wavelength_um=1.550,  # Red = -1
        name=f"opa_in_neg_{uid}"
    )
    opa_in_neg.dmove((0, -30))

    # Carry injector
    injector = c << carry_injector(name=f"injector_{uid}")
    injector.dmove((50, 0))

    # Combiner for pos and neg carry signals
    carry_combine = c << gf.components.mmi2x2()
    carry_combine.dmove((35, 0))

    route_single(c, cross_section=XS, port1=opa_in_pos.ports["output"], port2=carry_combine.ports["o1"])
    route_single(c, cross_section=XS, port1=opa_in_neg.ports["output"], port2=carry_combine.ports["o2"])
    route_single(c, cross_section=XS, port1=carry_combine.ports["o3"], port2=injector.ports["carry_in"])

    # === CARRY OUTPUT (to next trit) ===

    # Carry tap extracts carry wavelengths from mixer output
    tap = c << carry_tap(name=f"tap_{uid}")
    tap.dmove((150, 0))

    # OPA converters for outgoing carry
    opa_out_pos = c << wavelength_converter_opa(
        input_wavelength_um=0.500,
        output_wavelength_um=1.000,
        name=f"opa_out_pos_{uid}"
    )
    opa_out_pos.dmove((200, 30))

    opa_out_neg = c << wavelength_converter_opa(
        input_wavelength_um=0.775,
        output_wavelength_um=1.550,
        name=f"opa_out_neg_{uid}"
    )
    opa_out_neg.dmove((200, -30))

    # Delay lines for timing
    delay_pos = c << optical_delay_line(delay_ps=5.0, name=f"delay_pos_{uid}")
    delay_pos.dmove((250, 30))

    delay_neg = c << optical_delay_line(delay_ps=5.0, name=f"delay_neg_{uid}")
    delay_neg.dmove((250, -30))

    # Route carry tap outputs through OPA and delay
    route_single(c, cross_section=XS, port1=tap.ports["carry_pos"], port2=opa_out_pos.ports["input"])
    route_single(c, cross_section=XS, port1=tap.ports["carry_neg"], port2=opa_out_neg.ports["input"])
    route_single(c, cross_section=XS, port1=opa_out_pos.ports["output"], port2=delay_pos.ports["input"])
    route_single(c, cross_section=XS, port1=opa_out_neg.ports["output"], port2=delay_neg.ports["input"])

    # === PORTS ===

    # Carry inputs (from previous trit)
    c.add_port(name="carry_in_pos", port=opa_in_pos.ports["input"])
    c.add_port(name="carry_in_neg", port=opa_in_neg.ports["input"])

    # Signal path
    c.add_port(name="signal_in", port=injector.ports["signal_in"])
    c.add_port(name="to_mixer", port=injector.ports["output"])
    c.add_port(name="from_mixer", port=tap.ports["input"])
    c.add_port(name="to_detectors", port=tap.ports["thru"])

    # Carry outputs (to next trit)
    c.add_port(name="carry_out_pos", port=delay_pos.ports["output"])
    c.add_port(name="carry_out_neg", port=delay_neg.ports["output"])

    # Pump inputs for OPA
    c.add_port(name="pump_in_pos", port=opa_in_pos.ports["pump"])
    c.add_port(name="pump_in_neg", port=opa_in_neg.ports["pump"])
    c.add_port(name="pump_out_pos", port=opa_out_pos.ports["pump"])
    c.add_port(name="pump_out_neg", port=opa_out_neg.ports["pump"])

    c.add_label("OPTICAL_CARRY", position=(150, 50), layer=LABEL_LAYER)

    return c


# Layer for amplifier components
AMP_LAYER = (12, 0)


def semiconductor_optical_amplifier(
    length: float = 500.0,
    width: float = 2.0,
    gain_db: float = 20.0,
    name: str = "soa"
) -> gf.Component:
    """
    Creates a Semiconductor Optical Amplifier (SOA) for carry chain amplification.

    SOAs provide broadband amplification suitable for all wavelengths in the
    ternary encoding scheme. They are fast (ps switching) and compact.

    Typical specifications:
    - Gain: 15-25 dB
    - Bandwidth: >40 nm (covers 1.0-1.55 μm)
    - Saturation power: 10-15 dBm
    - Noise figure: 6-8 dB

    Structure:
        Input → Tapered coupler → Active region (InGaAsP/InP) → Tapered coupler → Output
                                        ↑
                                   Electrical bias

    Args:
        length: Active region length (μm)
        width: Active region width (μm)
        gain_db: Target gain in dB (for annotation)
        name: Component name
    """
    c = gf.Component(name)

    # Input taper (mode converter)
    taper_in = c << gf.components.taper(length=50, width1=0.5, width2=width)
    taper_in.dmove((0, 0))

    # Active gain region
    active = c << gf.components.straight(length=length, width=width)
    active.dmove((50, 0))

    # Output taper
    taper_out = c << gf.components.taper(length=50, width1=width, width2=0.5)
    taper_out.dmove((50 + length, 0))

    # Electrode pads for electrical bias
    pad_width = length * 0.8
    pad_height = 20
    c.add_polygon(
        [(50 + length * 0.1, width + 5),
         (50 + length * 0.9, width + 5),
         (50 + length * 0.9, width + 5 + pad_height),
         (50 + length * 0.1, width + 5 + pad_height)],
        layer=AMP_LAYER
    )

    # Ground plane
    c.add_polygon(
        [(50 + length * 0.1, -width - 5 - pad_height),
         (50 + length * 0.9, -width - 5 - pad_height),
         (50 + length * 0.9, -width - 5),
         (50 + length * 0.1, -width - 5)],
        layer=AMP_LAYER
    )

    # Labels
    c.add_label(f"SOA", position=(50 + length/2, width + 30), layer=LABEL_LAYER)
    c.add_label(f"+{gain_db:.0f}dB", position=(50 + length/2, -width - 30), layer=LABEL_LAYER)

    # Ports
    c.add_port(name="input", port=taper_in.ports["o1"])
    c.add_port(name="output", port=taper_out.ports["o2"])

    # Electrical bias port (for annotation)
    c.add_port(name="bias", center=(50 + length/2, width + 5 + pad_height), width=pad_width, orientation=90, layer=(1, 0))

    return c


def carry_chain_amplifier(
    gain_db: float = 25.0,
    name: str = "carry_amp"
) -> gf.Component:
    """
    Dual-channel amplifier for carry chain (positive and negative carry paths).

    Places two SOAs in parallel to amplify both carry signals simultaneously.
    Each SOA compensates for ~3 trits of carry loss (~25 dB).

    Structure:
        carry_pos_in ──→ SOA ──→ carry_pos_out
        carry_neg_in ──→ SOA ──→ carry_neg_out

    Args:
        gain_db: Target gain per channel in dB
        name: Component name
    """
    c = gf.Component(name)

    # SOA for positive carry
    soa_pos = c << semiconductor_optical_amplifier(
        length=500, gain_db=gain_db, name=f"{name}_soa_pos"
    )
    soa_pos.dmove((0, 50))

    # SOA for negative carry
    soa_neg = c << semiconductor_optical_amplifier(
        length=500, gain_db=gain_db, name=f"{name}_soa_neg"
    )
    soa_neg.dmove((0, -50))

    # Ports
    c.add_port(name="carry_pos_in", port=soa_pos.ports["input"])
    c.add_port(name="carry_pos_out", port=soa_pos.ports["output"])
    c.add_port(name="carry_neg_in", port=soa_neg.ports["input"])
    c.add_port(name="carry_neg_out", port=soa_neg.ports["output"])

    # Bias ports
    c.add_port(name="bias_pos", port=soa_pos.ports["bias"])
    c.add_port(name="bias_neg", port=soa_neg.ports["bias"])

    # Label
    c.add_label("CARRY_AMP", position=(300, 0), layer=LABEL_LAYER)
    c.add_label(f"+{gain_db:.0f}dB/ch", position=(300, -20), layer=LABEL_LAYER)

    return c


def wavelength_combiner(
    n_inputs: int = 3,
    name: str = "combiner"
) -> gf.Component:
    """
    Creates a wavelength combiner (multiplexer).

    Combines multiple wavelengths into a single waveguide.
    Uses cascaded Y-junctions or MMI.
    """
    c = gf.Component(name)

    if n_inputs == 2:
        # Simple 2x2 MMI used as combiner (2 in -> 1 out, ignore 4th port)
        mmi = c << gf.components.mmi2x2()
        c.add_port(name="in1", port=mmi.ports["o1"])
        c.add_port(name="in2", port=mmi.ports["o2"])
        c.add_port(name="output", port=mmi.ports["o3"])
    else:
        # Cascaded combiners for 3+ inputs
        # First combine inputs 1 and 2
        mmi1 = c << gf.components.mmi2x2()
        mmi1.dmove((0, 10))

        # Then combine with input 3
        mmi2 = c << gf.components.mmi2x2()
        mmi2.dmove((30, 0))

        # Route first combiner output to second combiner
        route_single(c, cross_section=XS, port1=mmi1.ports["o3"], port2=mmi2.ports["o1"])

        c.add_port(name="in1", port=mmi1.ports["o1"])
        c.add_port(name="in2", port=mmi1.ports["o2"])
        c.add_port(name="in3", port=mmi2.ports["o2"])
        c.add_port(name="output", port=mmi2.ports["o3"])

    return c


def wavelength_splitter(
    n_outputs: int = 3,
    name: str = "splitter"
) -> gf.Component:
    """
    Creates a wavelength splitter (demultiplexer / AWG-like).

    Splits input into separate wavelength channels.
    Supports 2, 3, 4, or 5 outputs via cascaded 1x2 MMIs.
    """
    c = gf.Component(name)

    if n_outputs == 2:
        mmi = c << gf.components.mmi1x2()
        c.add_port(name="input", port=mmi.ports["o1"])
        c.add_port(name="out1", port=mmi.ports["o2"])
        c.add_port(name="out2", port=mmi.ports["o3"])
    elif n_outputs == 3:
        # Cascaded splitters: 1->2, then one branch ->2 more
        mmi1 = c << gf.components.mmi1x2()
        mmi2 = c << gf.components.mmi1x2()
        mmi2.dmove((30, -10))

        route_single(c, cross_section=XS, port1=mmi1.ports["o3"], port2=mmi2.ports["o1"])

        c.add_port(name="input", port=mmi1.ports["o1"])
        c.add_port(name="out1", port=mmi1.ports["o2"])
        c.add_port(name="out2", port=mmi2.ports["o2"])
        c.add_port(name="out3", port=mmi2.ports["o3"])
    elif n_outputs == 4:
        # Binary tree: 1->2->4
        mmi1 = c << gf.components.mmi1x2()
        mmi2 = c << gf.components.mmi1x2()
        mmi3 = c << gf.components.mmi1x2()
        mmi2.dmove((30, 10))
        mmi3.dmove((30, -10))

        route_single(c, cross_section=XS, port1=mmi1.ports["o2"], port2=mmi2.ports["o1"])
        route_single(c, cross_section=XS, port1=mmi1.ports["o3"], port2=mmi3.ports["o1"])

        c.add_port(name="input", port=mmi1.ports["o1"])
        c.add_port(name="out1", port=mmi2.ports["o2"])
        c.add_port(name="out2", port=mmi2.ports["o3"])
        c.add_port(name="out3", port=mmi3.ports["o2"])
        c.add_port(name="out4", port=mmi3.ports["o3"])
    elif n_outputs == 5:
        # 1->2, then each ->2 (gives 4), then one more split on center
        # Structure: 1->2->4, plus one extra split = 5
        mmi1 = c << gf.components.mmi1x2()
        mmi2 = c << gf.components.mmi1x2()
        mmi3 = c << gf.components.mmi1x2()
        mmi4 = c << gf.components.mmi1x2()
        mmi2.dmove((30, 15))
        mmi3.dmove((30, -15))
        mmi4.dmove((60, -5))  # Extra split from mmi3 upper output

        route_single(c, cross_section=XS, port1=mmi1.ports["o2"], port2=mmi2.ports["o1"])
        route_single(c, cross_section=XS, port1=mmi1.ports["o3"], port2=mmi3.ports["o1"])
        route_single(c, cross_section=XS, port1=mmi3.ports["o2"], port2=mmi4.ports["o1"])

        c.add_port(name="input", port=mmi1.ports["o1"])
        c.add_port(name="out1", port=mmi2.ports["o2"])   # Top
        c.add_port(name="out2", port=mmi2.ports["o3"])
        c.add_port(name="out3", port=mmi4.ports["o2"])   # Center (from extra split)
        c.add_port(name="out4", port=mmi4.ports["o3"])
        c.add_port(name="out5", port=mmi3.ports["o3"])   # Bottom
    else:
        raise ValueError(f"n_outputs must be 2, 3, 4, or 5, got {n_outputs}")

    return c


def photodetector(
    width: float = 0.5,
    length: float = 2.0,
    name: str = "detector"
) -> gf.Component:
    """
    Creates a photodetector for reading output.
    """
    c = gf.Component(name)

    # Input taper
    taper = c << gf.components.taper(length=5, width1=0.5, width2=width)

    # Detector region (absorbing)
    det = c << gf.components.rectangle(size=(length, width), layer=(3, 0))
    det.dmove((5, -width/2))

    c.add_label("PD", position=(10, -width), layer=LABEL_LAYER)
    c.add_port(name="input", port=taper.ports["o1"])

    return c


def kerr_resonator(
    radius: float = 10.0,
    gap: float = 0.15,
    name: str = "kerr_clock"
) -> gf.Component:
    """
    Creates a Kerr resonator for optical clock/timing synchronization.

    The Kerr effect (third-order nonlinearity) creates self-phase modulation,
    enabling optical timing synchronization without electronics.

    Args:
        radius: Ring radius (larger = higher Q, sharper timing)
        gap: Coupling gap
        name: Component name
    """
    c = gf.Component(name)

    # Ring resonator with Kerr nonlinearity marker
    ring = c << gf.components.ring_single(radius=radius, gap=gap)

    # Visual marker for Kerr region (layer 5)
    c.add_polygon(
        [(- radius - 1, -1), (radius + 1, -1), (radius + 1, 1), (-radius - 1, 1)],
        layer=(5, 0)
    )

    c.add_label("CLK", position=(0, radius + 3), layer=LABEL_LAYER)

    c.add_port(name="input", port=ring.ports["o1"])
    c.add_port(name="output", port=ring.ports["o2"])

    return c


def y_junction(
    name: str = "y_split"
) -> gf.Component:
    """
    Creates a Y-junction beam splitter.

    Splits input beam into two equal-power outputs for A and B operand paths.
    Uses MMI-based 1x2 splitter for broadband operation.
    """
    c = gf.Component(name)

    # 1x2 MMI splitter
    mmi = c << gf.components.mmi1x2()

    c.add_label("Y", position=(0, 5), layer=LABEL_LAYER)

    c.add_port(name="input", port=mmi.ports["o1"])
    c.add_port(name="out_a", port=mmi.ports["o2"])
    c.add_port(name="out_b", port=mmi.ports["o3"])

    return c


def awg_demux(
    n_channels: int = 3,
    name: str = "awg"
) -> gf.Component:
    """
    Creates an Arrayed Waveguide Grating (AWG) demultiplexer.

    Separates input wavelengths into separate output channels.
    For ternary input: separates R (1.55um), G (1.216um), B (1.00um).
    For output detection: separates 5 SFG wavelengths (0.775, 0.681, 0.608, 0.549, 0.500 um).

    Args:
        n_channels: Number of output wavelength channels (3 or 5)
        name: Component name
    """
    c = gf.Component(name)

    if n_channels == 3:
        # 3-channel AWG for input demux (R/G/B)
        input_mmi = c << gf.components.mmi1x2()
        input_mmi.dmove((0, 0))

        mmi2 = c << gf.components.mmi1x2()
        mmi2.dmove((30, -10))

        route_single(c, cross_section=XS, port1=input_mmi.ports["o3"], port2=mmi2.ports["o1"])

        # AWG body marker (layer 6)
        c.add_polygon(
            [(10, -25), (50, -25), (50, 15), (10, 15)],
            layer=(6, 0)
        )
        c.add_label("AWG_3ch", position=(30, 20), layer=LABEL_LAYER)

        c.add_port(name="input", port=input_mmi.ports["o1"])
        c.add_port(name="out_1", port=input_mmi.ports["o2"])
        c.add_port(name="out_2", port=mmi2.ports["o2"])
        c.add_port(name="out_3", port=mmi2.ports["o3"])
        # Legacy port names for compatibility
        c.add_port(name="out_r", port=input_mmi.ports["o2"])
        c.add_port(name="out_g", port=mmi2.ports["o2"])
        c.add_port(name="out_b", port=mmi2.ports["o3"])

    elif n_channels == 5:
        # 5-channel AWG for output demux (SFG wavelengths)
        # Structure: 1->2->4, then one branch splits again for 5th channel
        mmi1 = c << gf.components.mmi1x2()
        mmi2 = c << gf.components.mmi1x2()
        mmi3 = c << gf.components.mmi1x2()
        mmi4 = c << gf.components.mmi1x2()

        mmi1.dmove((0, 0))
        mmi2.dmove((30, 12))
        mmi3.dmove((30, -12))
        mmi4.dmove((60, 0))

        route_single(c, cross_section=XS, port1=mmi1.ports["o2"], port2=mmi2.ports["o1"])
        route_single(c, cross_section=XS, port1=mmi1.ports["o3"], port2=mmi3.ports["o1"])
        route_single(c, cross_section=XS, port1=mmi3.ports["o2"], port2=mmi4.ports["o1"])

        # AWG body marker (layer 6) - larger for 5-channel
        c.add_polygon(
            [(5, -30), (80, -30), (80, 30), (5, 30)],
            layer=(6, 0)
        )
        c.add_label("AWG_5ch", position=(40, 35), layer=LABEL_LAYER)

        c.add_port(name="input", port=mmi1.ports["o1"])
        c.add_port(name="out_1", port=mmi2.ports["o2"])   # 0.775 μm (DET_-2)
        c.add_port(name="out_2", port=mmi2.ports["o3"])   # 0.681 μm (DET_-1)
        c.add_port(name="out_3", port=mmi4.ports["o2"])   # 0.608 μm (DET_0)
        c.add_port(name="out_4", port=mmi4.ports["o3"])   # 0.549 μm (DET_+1)
        c.add_port(name="out_5", port=mmi3.ports["o3"])   # 0.500 μm (DET_+2)

    else:
        raise ValueError(f"n_channels must be 3 or 5, got {n_channels}")

    return c


def ternary_output_stage_simple(
    name: str = "output_simple",
    uid: str = "",
    include_carry_ports: bool = False
) -> gf.Component:
    """
    SIMPLIFIED output stage using single AWG demux instead of 5 ring filters.

    Structure: Input -> AWG (5-ch) -> 5x Photodetectors

    This replaces:
      - 1x 5-way splitter
      - 5x ring resonator filters
    With:
      - 1x 5-channel AWG demux

    Component reduction: 6 components -> 1 component (per ALU)
    Total savings for 81 ALUs: 405 ring resonators eliminated

    Output channels (SFG wavelengths):
      - Ch1 (0.775 μm): Result = -2 (borrow) -> CARRY_OUT_NEG
      - Ch2 (0.681 μm): Result = -1
      - Ch3 (0.608 μm): Result = 0
      - Ch4 (0.549 μm): Result = +1
      - Ch5 (0.500 μm): Result = +2 (carry) -> CARRY_OUT_POS

    Args:
        include_carry_ports: If True, adds electrical carry output pads for
                            carry chain wiring between adjacent trits.

    Carry Chain (Electronic Approach):
    ---------------------------------
    The DET_-2 (borrow) and DET_+2 (carry) photodetector outputs are
    exposed as electrical pads (CARRY_OUT_NEG, CARRY_OUT_POS) that can
    be wired to firmware GPIO or the next trit's carry input.

    Firmware Carry Propagation Algorithm:
      1. Read all photodetector outputs simultaneously
      2. For each trit position N (from LSB to MSB):
         a. Check CARRY_OUT_POS from trit N-1: if active, add +1 to current sum
         b. Check CARRY_OUT_NEG from trit N-1: if active, add -1 to current sum
      3. The result at each trit is: A[N] + B[N] + carry_in mod 3
      4. Generate new carry for trit N+1

    Signal Naming Convention:
      - CARRY_OUT_POS: Positive overflow (+2 detected) -> add +1 to next trit
      - CARRY_OUT_NEG: Negative overflow (-2 detected) -> add -1 to next trit (borrow)
      - CARRY_IN: Combined carry input from previous trit (active-high logic)
    """
    import uuid
    if not uid:
        uid = str(uuid.uuid4())[:8]

    c = gf.Component(name)

    # Single 5-channel AWG demux replaces splitter + 5 ring filters
    awg = c << awg_demux(n_channels=5, name=f"awg_out_{uid}")

    # 5 photodetectors directly connected to AWG outputs
    DETECTOR_CONFIG = [
        {'value': -2, 'wavelength_um': 0.775, 'name': 'Neg2', 'port': 'out_1', 'is_carry': True},
        {'value': -1, 'wavelength_um': 0.681, 'name': 'Neg1', 'port': 'out_2', 'is_carry': False},
        {'value':  0, 'wavelength_um': 0.608, 'name': 'Zero', 'port': 'out_3', 'is_carry': False},
        {'value': +1, 'wavelength_um': 0.549, 'name': 'Pos1', 'port': 'out_4', 'is_carry': False},
        {'value': +2, 'wavelength_um': 0.500, 'name': 'Pos2', 'port': 'out_5', 'is_carry': True},
    ]

    y_positions = [24, 12, 0, -12, -24]  # Match AWG output positions

    for i, det_info in enumerate(DETECTOR_CONFIG):
        det = c << photodetector(
            width=0.5,
            length=2.0,
            name=f"det_{det_info['name']}_{uid}"
        )
        det.dmove((95, y_positions[i]))

        # Route AWG output directly to detector
        route_single(c, cross_section=XS,
                    port1=awg.ports[det_info['port']],
                    port2=det.ports["input"])

        # Label
        label_suffix = "_C" if det_info['is_carry'] else ""
        c.add_label(f"D{det_info['value']:+d}{label_suffix}",
                   position=(110, y_positions[i]), layer=LABEL_LAYER)

    # Input port
    c.add_port(name="input", port=awg.ports["input"])

    # Add electrical carry output pads if requested
    if include_carry_ports:
        # CARRY_OUT_NEG pad: electrical output from DET_-2 (borrow signal)
        # Position: right side of DET_-2, top of output stage
        c.add_polygon(
            [(120, y_positions[0] - 3), (130, y_positions[0] - 3),
             (130, y_positions[0] + 3), (120, y_positions[0] + 3)],
            layer=HEATER_LAYER  # Using heater layer for electrical pads
        )
        c.add_label("CARRY_OUT_NEG", position=(125, y_positions[0] + 7), layer=LABEL_LAYER)

        # CARRY_OUT_POS pad: electrical output from DET_+2 (carry signal)
        # Position: right side of DET_+2, bottom of output stage
        c.add_polygon(
            [(120, y_positions[4] - 3), (130, y_positions[4] - 3),
             (130, y_positions[4] + 3), (120, y_positions[4] + 3)],
            layer=HEATER_LAYER
        )
        c.add_label("CARRY_OUT_POS", position=(125, y_positions[4] - 9), layer=LABEL_LAYER)

        # CARRY_IN pad: electrical input for carry from previous trit
        # Position: left side of output stage, near optical input
        c.add_polygon(
            [(-15, -3), (-5, -3), (-5, 3), (-15, 3)],
            layer=HEATER_LAYER
        )
        c.add_label("CARRY_IN", position=(-10, 7), layer=LABEL_LAYER)

    c.add_label("OUT_AWG", position=(50, 40), layer=LABEL_LAYER)

    return c


def optical_frontend(
    name: str = "frontend",
    uid: str = ""
) -> gf.Component:
    """
    Creates the complete optical frontend/input conditioning stage.

    Structure:
      CW Laser Input -> Kerr Resonator (clock) -> Y-Junction (split A/B)
                                                      |
                                          +-----------+-----------+
                                          |                       |
                                        AWG_A                   AWG_B
                                       (demux)                 (demux)
                                          |                       |
                                    R_A, G_A, B_A           R_B, G_B, B_B

    Returns component with ports for laser input and 6 wavelength outputs
    (3 for operand A, 3 for operand B).
    """
    import uuid
    if not uid:
        uid = str(uuid.uuid4())[:8]

    c = gf.Component(name)

    # 1. Kerr resonator for timing
    clk = c << kerr_resonator(name=f"clk_{uid}")
    clk.dmove((0, 0))

    # 2. Y-junction to split to A and B paths
    ysplit = c << y_junction(name=f"ysplit_{uid}")
    ysplit.dmove((40, 0))

    route_single(c, cross_section=XS, port1=clk.ports["output"], port2=ysplit.ports["input"])

    # 3. AWG for operand A (upper path)
    awg_a = c << awg_demux(name=f"awg_a_{uid}")
    awg_a.dmove((80, 30))

    route_single(c, cross_section=XS, port1=ysplit.ports["out_a"], port2=awg_a.ports["input"])

    # 4. AWG for operand B (lower path)
    awg_b = c << awg_demux(name=f"awg_b_{uid}")
    awg_b.dmove((80, -30))

    route_single(c, cross_section=XS, port1=ysplit.ports["out_b"], port2=awg_b.ports["input"])

    # Labels
    c.add_label("FRONTEND", position=(60, 60), layer=LABEL_LAYER)
    c.add_label("CW_IN", position=(-15, 0), layer=LABEL_LAYER)

    # Ports
    c.add_port(name="laser_in", port=clk.ports["input"])

    # Operand A outputs
    c.add_port(name="a_red", port=awg_a.ports["out_r"])
    c.add_port(name="a_green", port=awg_a.ports["out_g"])
    c.add_port(name="a_blue", port=awg_a.ports["out_b"])

    # Operand B outputs
    c.add_port(name="b_red", port=awg_b.ports["out_r"])
    c.add_port(name="b_green", port=awg_b.ports["out_g"])
    c.add_port(name="b_blue", port=awg_b.ports["out_b"])

    return c


def ternary_output_stage(
    name: str = "output_stage",
    uid: str = "",
    include_carry: bool = True
) -> gf.Component:
    """
    Creates a wavelength-discriminating output stage for SFG mixer results.

    Structure: Input -> Splitter -> 5x Filters -> 5x Photodetectors

    The mixer SFG output hits all five filtered detectors simultaneously.
    Each detector is tuned to a specific SFG OUTPUT wavelength (not input wavelength).

    Full detector mapping (all 5 results, verified by simulation):
      - Det -2 (0.775 μm): Result = -2 (from R+R mixing) - CARRY/BORROW
      - Det -1 (0.681 μm): Result = -1 (from R+G mixing)
      - Det  0 (0.608 μm): Result =  0 (from R+B or G+G mixing)
      - Det +1 (0.549 μm): Result = +1 (from G+B mixing)
      - Det +2 (0.500 μm): Result = +2 (from B+B mixing) - CARRY

    Args:
        include_carry: If True, includes all 5 detectors (-2 to +2).
                      If False, only 3 detectors (-1, 0, +1).
    """
    import uuid
    if not uid:
        uid = str(uuid.uuid4())[:8]

    c = gf.Component(name)

    # Full detector configuration for all 5 SFG output wavelengths (verified by simulation)
    DETECTOR_CONFIG_FULL = [
        {'value': -2, 'wavelength_um': 0.775, 'name': 'Neg2', 'is_carry': True},   # R+R → -2 (borrow)
        {'value': -1, 'wavelength_um': 0.681, 'name': 'Neg1', 'is_carry': False},  # R+G → -1
        {'value':  0, 'wavelength_um': 0.608, 'name': 'Zero', 'is_carry': False},  # R+B or G+G → 0
        {'value': +1, 'wavelength_um': 0.549, 'name': 'Pos1', 'is_carry': False},  # G+B → +1
        {'value': +2, 'wavelength_um': 0.500, 'name': 'Pos2', 'is_carry': True},   # B+B → +2 (carry)
    ]

    DETECTOR_CONFIG_BASIC = [
        {'value': -1, 'wavelength_um': 0.681, 'name': 'Neg1', 'is_carry': False},
        {'value':  0, 'wavelength_um': 0.608, 'name': 'Zero', 'is_carry': False},
        {'value': +1, 'wavelength_um': 0.549, 'name': 'Pos1', 'is_carry': False},
    ]

    detector_config = DETECTOR_CONFIG_FULL if include_carry else DETECTOR_CONFIG_BASIC
    n_detectors = len(detector_config)

    # Splitter to send light to all detector paths
    splitter = c << wavelength_splitter(n_outputs=n_detectors, name=f"output_split_{uid}")

    # Filtered detector channels
    y_spacing = 25
    detector_x = 100 if include_carry else 80
    center_index = n_detectors // 2

    for i, det_info in enumerate(detector_config):
        y_pos = (i - center_index) * y_spacing

        # Ring resonator filter tuned to SFG output wavelength
        filt = c << wavelength_selector(
            wavelength_um=det_info['wavelength_um'],
            radius=5.0,
            gap=0.15,
            name=f"filter_{det_info['name']}_{uid}"
        )
        filt.dmove((50, y_pos))

        # Photodetector after filter
        det = c << photodetector(
            width=0.5,
            length=2.0,
            name=f"detect_{det_info['name']}_{uid}"
        )
        det.dmove((detector_x, y_pos))

        # Route splitter -> filter -> detector
        route_single(c, cross_section=XS,
                    port1=splitter.ports[f"out{i+1}"],
                    port2=filt.ports["input"])
        route_single(c, cross_section=XS,
                    port1=filt.ports["output"],
                    port2=det.ports["input"])

        # Label each detector with result value (mark carry/borrow)
        label_suffix = "_C" if det_info['is_carry'] else ""
        c.add_label(f"DET_{det_info['value']:+d}{label_suffix}",
                   position=(detector_x + 15, y_pos), layer=LABEL_LAYER)

    # Input port
    c.add_port(name="input", port=splitter.ports["input"])

    # Labels
    c.add_label("OUT_FULL" if include_carry else "OUT",
               position=(60, (center_index + 1) * y_spacing), layer=LABEL_LAYER)

    return c


# =============================================================================
# HIGH-LEVEL CHIP GENERATORS
# =============================================================================

def ternary_input_stage(
    operand_name: str = "A",
    y_offset: float = 0,
    uid: str = "",
    selector_type: Literal['ring', 'mzi'] = 'ring'
) -> gf.Component:
    """
    Creates an input stage for one ternary operand.

    Structure: Input -> Splitter -> 3x Selectors (R/G/B)
    Each selector can be individually enabled to set the ternary value.

    Args:
        operand_name: Name for this operand (e.g., "A" or "B")
        y_offset: Vertical offset for positioning
        uid: Unique identifier suffix
        selector_type: Type of wavelength selector to use:
            - 'ring': Ring resonator (default, wavelength-selective)
            - 'mzi': MZI switch (better extinction, broader bandwidth)
    """
    c = gf.Component(f"input_{operand_name}_{uid}")

    # Input splitter (1 -> 3 wavelengths)
    splitter = c << wavelength_splitter(n_outputs=3, name=f"split_{operand_name}_{uid}")

    # Three selectors for R, G, B
    y_spacing = 30 if selector_type == 'ring' else 40  # MZI needs more vertical space
    x_offset = 60 if selector_type == 'ring' else 60
    selectors = []

    for i, (trit, info) in enumerate(TERNARY_ENCODING.items()):
        if selector_type == 'mzi':
            sel = c << wavelength_selector_mzi(
                wavelength_um=info['wavelength_um'],
                name=f"sel_{operand_name}_{info['name']}_{uid}"
            )
        else:
            sel = c << wavelength_selector(
                wavelength_um=info['wavelength_um'],
                name=f"sel_{operand_name}_{info['name']}_{uid}"
            )
        sel.dmove((x_offset, (i - 1) * y_spacing))
        selectors.append(sel)

        # Route splitter to selector
        route_single(c, cross_section=XS, port1=splitter.ports[f"out{i+1}"], port2=sel.ports["input"])

    # Combiner to merge selected wavelengths
    combiner_x = 130 if selector_type == 'ring' else 180  # MZI is wider
    combiner = c << wavelength_combiner(n_inputs=3, name=f"comb_{operand_name}_{uid}")
    combiner.dmove((combiner_x, 0))

    # Route selectors to combiner
    for i, sel in enumerate(selectors):
        route_single(c, cross_section=XS, port1=sel.ports["output"], port2=combiner.ports[f"in{i+1}"])

    # Final output port
    c.add_port(name="input", port=splitter.ports["input"])
    c.add_port(name="output", port=combiner.ports["output"])

    # Move entire stage
    c.dmove((0, y_offset))

    return c


def generate_ternary_alu(
    operations: List[str] = ["add"],
    name: str = "TernaryALU",
    selector_type: Literal['ring', 'mzi'] = 'ring'
) -> gf.Component:
    """
    Generates a complete Ternary ALU chip.

    Args:
        operations: List of operations to support ['add', 'multiply', 'compare']
        name: Chip name
        selector_type: Type of wavelength selector to use:
            - 'ring': Ring resonator (default, wavelength-selective)
            - 'mzi': MZI switch (better extinction ratio, broader bandwidth,
                     more tolerant to fabrication variations)

    Returns:
        Complete chip layout
    """
    import uuid
    uid = str(uuid.uuid4())[:8]

    c = gf.Component(name)

    # =========================
    # 1. INPUT STAGES (2 operands)
    # =========================
    input_a = c << ternary_input_stage("A", y_offset=50, uid=uid, selector_type=selector_type)
    input_b = c << ternary_input_stage("B", y_offset=-50, uid=uid, selector_type=selector_type)

    # =========================
    # 2. OPERATION COMBINER
    # =========================
    # Merge both operands into single waveguide for mixing
    op_combiner = c << gf.components.mmi2x2()
    op_combiner.dmove((200, 0))

    route_single(c, cross_section=XS, port1=input_a.ports["output"], port2=op_combiner.ports["o2"])
    route_single(c, cross_section=XS, port1=input_b.ports["output"], port2=op_combiner.ports["o3"])

    # =========================
    # 3. SFG MIXER (The brain!)
    # =========================
    mixer = c << sfg_mixer(length=20, name=f"alu_mixer_{uid}")
    mixer.dmove((250, 0))

    route_single(c, cross_section=XS, port1=op_combiner.ports["o1"], port2=mixer.ports["input"])

    # =========================
    # 4. OUTPUT DETECTION (3-channel)
    # =========================
    output_stage = c << ternary_output_stage(name=f"output_{uid}", uid=uid)
    output_stage.dmove((300, 0))

    route_single(c, cross_section=XS, port1=mixer.ports["output"], port2=output_stage.ports["input"])

    # =========================
    # 5. LABELS & METADATA
    # =========================
    c.add_label("ALU", position=(150, 100), layer=LABEL_LAYER)
    c.add_label("A", position=(0, 80), layer=LABEL_LAYER)
    c.add_label("B", position=(0, -80), layer=LABEL_LAYER)
    c.add_label("Q", position=(300, 40), layer=LABEL_LAYER)

    # Add input ports
    c.add_port(name="input_a", port=input_a.ports["input"])
    c.add_port(name="input_b", port=input_b.ports["input"])

    return c


def generate_ternary_adder() -> gf.Component:
    """
    Generates a ternary adder chip.

    Truth table (simplified):
      A + B = Result
     -1 + -1 = -2 (overflow to -1 with carry)
     -1 +  0 = -1
     -1 + +1 =  0
      0 + -1 = -1
      0 +  0 =  0
      0 + +1 = +1
     +1 + -1 =  0
     +1 +  0 = +1
     +1 + +1 = +2 (overflow to +1 with carry)
    """
    return generate_ternary_alu(operations=["add"], name="TernaryAdder")


def generate_ternary_subtractor() -> gf.Component:
    """
    Generates a ternary subtractor chip.

    A - B is implemented as A + (-B) where -B swaps Red↔Blue wavelengths.

    Truth table:
      A - B = Result
     -1 - -1 =  0
     -1 -  0 = -1
     -1 - +1 = -2 (overflow)
      0 - -1 = +1
      0 -  0 =  0
      0 - +1 = -1
     +1 - -1 = +2 (overflow)
     +1 -  0 = +1
     +1 - +1 =  0
    """
    return generate_ternary_alu(operations=["subtract"], name="TernarySubtractor")


def generate_ternary_divider() -> gf.Component:
    """
    Generates a ternary divider chip.

    Uses DFG (Difference Frequency Generation) for division.
    Note: Integer division in ternary, rounds toward zero.

    This is a single-trit divider. Multi-trit division requires
    cascaded stages with feedback.
    """
    return generate_ternary_alu(operations=["divide"], name="TernaryDivider")


def generate_ternary_multiplier() -> gf.Component:
    """
    Generates a ternary multiplier chip.

    Uses SFG mixing where wavelength multiplication corresponds to
    frequency addition, mapping to ternary value multiplication.
    """
    return generate_ternary_alu(operations=["multiply"], name="TernaryMultiplier")


def generate_full_processor(
    n_trits: int = 3,
    name: str = "TernaryProcessor"
) -> gf.Component:
    """
    Generates a complete N-trit ternary processor.

    Args:
        n_trits: Number of trits per operand (3 = 27 values, 9 = 19683 values)
        name: Chip name
    """
    import uuid
    c = gf.Component(name)

    # Create array of ALU units
    y_spacing = 200

    for i in range(n_trits):
        # Use unique ID suffix to avoid name collisions
        uid = str(uuid.uuid4())[:8]
        alu = c << generate_ternary_alu(
            operations=["add", "multiply"],
            name=f"ALU_trit{i}_{uid}"
        )
        alu.dmove((0, i * y_spacing))

    c.add_label(f"CPU_{n_trits}T", position=(150, n_trits * y_spacing + 50), layer=LABEL_LAYER)

    return c


def generate_complete_alu(
    name: str = "TernaryComplete",
    simplified_output: bool = True,
    operation: Literal['add', 'sub', 'mul'] = 'add',
    selector_type: Literal['ring', 'mzi'] = 'ring'
) -> gf.Component:
    """
    Generates a complete single-trit ALU with optical frontend and output stage.

    Complete signal path:
      CW Laser → Kerr Clock → Y-Split → AWG_A → Selectors_A → Combiner
                                     → AWG_B → Selectors_B → Combiner
                                                                  ↓
                                                            Mixer (SFG/DFG/MUL)
                                                                  ↓
                                                         Output Stage (5 detectors)
                                                                  ↓
                                                         DET_-2 to DET_+2

    Args:
        name: Component name.
        simplified_output: If True, uses single AWG demux (fewer components).
                          If False, uses 5 ring filters (more precise but complex).
        operation: The arithmetic operation to perform:
                   - 'add': Addition using SFG (Sum Frequency Generation)
                   - 'sub': Subtraction using DFG (Difference Frequency Generation)
                   - 'mul': Multiplication using Kerr effect (χ³ nonlinearity)
        selector_type: Type of wavelength selector to use:
                   - 'ring': Ring resonator (default, wavelength-selective)
                   - 'mzi': MZI switch (better extinction ratio, broader bandwidth,
                            more tolerant to fabrication variations, voltage-tuned)
    """
    import uuid
    uid = str(uuid.uuid4())[:8]

    c = gf.Component(name)

    # =========================
    # 1. OPTICAL FRONTEND
    # =========================
    frontend = c << optical_frontend(name=f"frontend_{uid}", uid=uid)
    frontend.dmove((0, 0))

    # =========================
    # 2. INPUT SELECTORS FOR A
    # =========================
    # Three selectors for R, G, B on operand A
    # Selector function and positioning based on selector_type
    if selector_type == 'mzi':
        sel_a_r = c << wavelength_selector_mzi(wavelength_um=1.550, name=f"sel_a_r_{uid}")
        sel_a_g = c << wavelength_selector_mzi(wavelength_um=1.216, name=f"sel_a_g_{uid}")
        sel_a_b = c << wavelength_selector_mzi(wavelength_um=1.000, name=f"sel_a_b_{uid}")
        # MZI needs more spacing due to larger footprint
        sel_a_r.dmove((200, 80))
        sel_a_g.dmove((200, 40))
        sel_a_b.dmove((200, 0))
        comb_a_x = 320  # Combiner positioned further for MZI
        comb_a_y = 40
    else:
        sel_a_r = c << wavelength_selector(wavelength_um=1.550, name=f"sel_a_r_{uid}")
        sel_a_g = c << wavelength_selector(wavelength_um=1.216, name=f"sel_a_g_{uid}")
        sel_a_b = c << wavelength_selector(wavelength_um=1.000, name=f"sel_a_b_{uid}")
        sel_a_r.dmove((200, 60))
        sel_a_g.dmove((200, 30))
        sel_a_b.dmove((200, 0))
        comb_a_x = 280
        comb_a_y = 30

    # Route frontend AWG_A outputs to selectors
    route_single(c, cross_section=XS, port1=frontend.ports["a_red"], port2=sel_a_r.ports["input"])
    route_single(c, cross_section=XS, port1=frontend.ports["a_green"], port2=sel_a_g.ports["input"])
    route_single(c, cross_section=XS, port1=frontend.ports["a_blue"], port2=sel_a_b.ports["input"])

    # Combiner for A
    comb_a = c << wavelength_combiner(n_inputs=3, name=f"comb_a_{uid}")
    comb_a.dmove((comb_a_x, comb_a_y))

    route_single(c, cross_section=XS, port1=sel_a_r.ports["output"], port2=comb_a.ports["in1"])
    route_single(c, cross_section=XS, port1=sel_a_g.ports["output"], port2=comb_a.ports["in2"])
    route_single(c, cross_section=XS, port1=sel_a_b.ports["output"], port2=comb_a.ports["in3"])

    # =========================
    # 3. INPUT SELECTORS FOR B
    # =========================
    if selector_type == 'mzi':
        sel_b_r = c << wavelength_selector_mzi(wavelength_um=1.550, name=f"sel_b_r_{uid}")
        sel_b_g = c << wavelength_selector_mzi(wavelength_um=1.216, name=f"sel_b_g_{uid}")
        sel_b_b = c << wavelength_selector_mzi(wavelength_um=1.000, name=f"sel_b_b_{uid}")
        # MZI needs more spacing
        sel_b_r.dmove((200, -40))
        sel_b_g.dmove((200, -80))
        sel_b_b.dmove((200, -120))
        comb_b_x = 320
        comb_b_y = -80
    else:
        sel_b_r = c << wavelength_selector(wavelength_um=1.550, name=f"sel_b_r_{uid}")
        sel_b_g = c << wavelength_selector(wavelength_um=1.216, name=f"sel_b_g_{uid}")
        sel_b_b = c << wavelength_selector(wavelength_um=1.000, name=f"sel_b_b_{uid}")
        sel_b_r.dmove((200, -60))
        sel_b_g.dmove((200, -30))
        sel_b_b.dmove((200, 0 - 60))
        comb_b_x = 280
        comb_b_y = -60

    # Route frontend AWG_B outputs to selectors
    route_single(c, cross_section=XS, port1=frontend.ports["b_red"], port2=sel_b_r.ports["input"])
    route_single(c, cross_section=XS, port1=frontend.ports["b_green"], port2=sel_b_g.ports["input"])
    route_single(c, cross_section=XS, port1=frontend.ports["b_blue"], port2=sel_b_b.ports["input"])

    # Combiner for B
    comb_b = c << wavelength_combiner(n_inputs=3, name=f"comb_b_{uid}")
    comb_b.dmove((comb_b_x, comb_b_y))

    route_single(c, cross_section=XS, port1=sel_b_r.ports["output"], port2=comb_b.ports["in1"])
    route_single(c, cross_section=XS, port1=sel_b_g.ports["output"], port2=comb_b.ports["in2"])
    route_single(c, cross_section=XS, port1=sel_b_b.ports["output"], port2=comb_b.ports["in3"])

    # =========================
    # 4. OPERATION COMBINER
    # =========================
    op_combiner = c << gf.components.mmi2x2()
    op_combiner.dmove((380, 0))

    route_single(c, cross_section=XS, port1=comb_a.ports["output"], port2=op_combiner.ports["o1"])
    route_single(c, cross_section=XS, port1=comb_b.ports["output"], port2=op_combiner.ports["o2"])

    # =========================
    # 5. MIXER (operation-dependent)
    # =========================
    # Select mixer type based on operation
    if operation == 'add':
        # SFG mixer for addition: λ_out = 1/(1/λ1 + 1/λ2)
        mixer = c << sfg_mixer(length=20, name=f"sfg_mixer_{uid}")
        op_label = "ADD_SFG"
    elif operation == 'sub':
        # DFG mixer for subtraction: λ_out = 1/(1/λ1 - 1/λ2)
        mixer = c << dfg_mixer(length=25, name=f"dfg_mixer_{uid}")
        op_label = "SUB_DFG"
    elif operation == 'mul':
        # Kerr/χ³ mixer for multiplication
        mixer = c << mul_mixer(length=30, name=f"mul_mixer_{uid}")
        op_label = "MUL_KERR"
    else:
        raise ValueError(f"Unknown operation '{operation}'. Must be 'add', 'sub', or 'mul'.")

    mixer.dmove((430, 0))

    route_single(c, cross_section=XS, port1=op_combiner.ports["o3"], port2=mixer.ports["input"])

    # =========================
    # 6. OUTPUT STAGE (5 detectors)
    # =========================
    if simplified_output:
        output = c << ternary_output_stage_simple(name=f"output_{uid}", uid=uid)
    else:
        output = c << ternary_output_stage(name=f"output_{uid}", uid=uid)
    output.dmove((480, 0))

    route_single(c, cross_section=XS, port1=mixer.ports["output"], port2=output.ports["input"])

    # =========================
    # 7. LABELS
    # =========================
    c.add_label(f"ALU_{op_label}", position=(250, 100), layer=LABEL_LAYER)
    c.add_label("LASER_IN", position=(-20, 0), layer=LABEL_LAYER)

    # Add port for laser input
    c.add_port(name="laser_in", port=frontend.ports["laser_in"])

    return c


def generate_optical_carry_alu(
    name: str = "TernaryOpticalCarry",
    operation: Literal['add', 'sub', 'mul'] = 'add',
    selector_type: Literal['ring', 'mzi'] = 'ring'
) -> gf.Component:
    """
    Generates a single-trit ALU with FULLY OPTICAL carry propagation.

    This ALU includes the optical carry chain components:
      - Carry input (from previous trit) via OPA wavelength conversion
      - Carry output (to next trit) via carry tap + OPA + delay line

    The carry signals are wavelength-converted and time-delayed so that
    multi-trit arithmetic happens entirely in the optical domain.
    The controlling computer just loads operands and reads results.

    Signal flow:
      carry_in_pos ──→ OPA ──┐
      carry_in_neg ──→ OPA ──┼→ Injector ──┐
                             │             │
      CW Laser → Frontend → AWG → Selectors → Combiner ──→ Injector → Mixer
                                                                        ↓
      carry_out_pos ←── OPA ←── Delay ←── Carry Tap ←── Mixer Output
      carry_out_neg ←── OPA ←── Delay ←──────┘              ↓
                                                      Output Stage
                                                           ↓
                                                    DET_-2 to DET_+2

    Args:
        name: Component name
        operation: 'add', 'sub', or 'mul'
        selector_type: 'ring' or 'mzi'
    """
    import uuid
    uid = str(uuid.uuid4())[:8]

    c = gf.Component(name)

    # =========================
    # 1. OPTICAL FRONTEND
    # =========================
    frontend = c << optical_frontend(name=f"frontend_{uid}", uid=uid)
    frontend.dmove((0, 0))

    # =========================
    # 2. WAVELENGTH SELECTORS FOR OPERAND A
    # =========================
    if selector_type == 'ring':
        sel_a_r = c << wavelength_selector(wavelength_um=1.550, name=f"sel_a_r_{uid}")
        sel_a_g = c << wavelength_selector(wavelength_um=1.216, name=f"sel_a_g_{uid}")
        sel_a_b = c << wavelength_selector(wavelength_um=1.000, name=f"sel_a_b_{uid}")
    else:  # mzi
        sel_a_r = c << wavelength_selector_mzi(wavelength_um=1.550, name=f"sel_a_r_{uid}")
        sel_a_g = c << wavelength_selector_mzi(wavelength_um=1.216, name=f"sel_a_g_{uid}")
        sel_a_b = c << wavelength_selector_mzi(wavelength_um=1.000, name=f"sel_a_b_{uid}")

    sel_a_r.dmove((180, 50))
    sel_a_g.dmove((180, 25))
    sel_a_b.dmove((180, 0))

    route_single(c, cross_section=XS, port1=frontend.ports["a_red"], port2=sel_a_r.ports["input"])
    route_single(c, cross_section=XS, port1=frontend.ports["a_green"], port2=sel_a_g.ports["input"])
    route_single(c, cross_section=XS, port1=frontend.ports["a_blue"], port2=sel_a_b.ports["input"])

    # Combiner for A
    comb_a = c << wavelength_combiner(n_inputs=3, name=f"comb_a_{uid}")
    comb_a.dmove((280, 25))

    route_single(c, cross_section=XS, port1=sel_a_r.ports["output"], port2=comb_a.ports["in1"])
    route_single(c, cross_section=XS, port1=sel_a_g.ports["output"], port2=comb_a.ports["in2"])
    route_single(c, cross_section=XS, port1=sel_a_b.ports["output"], port2=comb_a.ports["in3"])

    # =========================
    # 3. WAVELENGTH SELECTORS FOR OPERAND B
    # =========================
    if selector_type == 'ring':
        sel_b_r = c << wavelength_selector(wavelength_um=1.550, name=f"sel_b_r_{uid}")
        sel_b_g = c << wavelength_selector(wavelength_um=1.216, name=f"sel_b_g_{uid}")
        sel_b_b = c << wavelength_selector(wavelength_um=1.000, name=f"sel_b_b_{uid}")
    else:  # mzi
        sel_b_r = c << wavelength_selector_mzi(wavelength_um=1.550, name=f"sel_b_r_{uid}")
        sel_b_g = c << wavelength_selector_mzi(wavelength_um=1.216, name=f"sel_b_g_{uid}")
        sel_b_b = c << wavelength_selector_mzi(wavelength_um=1.000, name=f"sel_b_b_{uid}")

    sel_b_r.dmove((180, -25))
    sel_b_g.dmove((180, -50))
    sel_b_b.dmove((180, -75))

    route_single(c, cross_section=XS, port1=frontend.ports["b_red"], port2=sel_b_r.ports["input"])
    route_single(c, cross_section=XS, port1=frontend.ports["b_green"], port2=sel_b_g.ports["input"])
    route_single(c, cross_section=XS, port1=frontend.ports["b_blue"], port2=sel_b_b.ports["input"])

    # Combiner for B
    comb_b = c << wavelength_combiner(n_inputs=3, name=f"comb_b_{uid}")
    comb_b.dmove((280, -50))

    route_single(c, cross_section=XS, port1=sel_b_r.ports["output"], port2=comb_b.ports["in1"])
    route_single(c, cross_section=XS, port1=sel_b_g.ports["output"], port2=comb_b.ports["in2"])
    route_single(c, cross_section=XS, port1=sel_b_b.ports["output"], port2=comb_b.ports["in3"])

    # =========================
    # 4. OPERATION COMBINER (A + B)
    # =========================
    op_combiner = c << gf.components.mmi2x2()
    op_combiner.dmove((380, -10))

    route_single(c, cross_section=XS, port1=comb_a.ports["output"], port2=op_combiner.ports["o1"])
    route_single(c, cross_section=XS, port1=comb_b.ports["output"], port2=op_combiner.ports["o2"])

    # =========================
    # 5. OPTICAL CARRY CHAIN
    # =========================
    carry_unit = c << optical_carry_unit(name=f"carry_{uid}", uid=uid)
    carry_unit.dmove((420, -10))

    # Route operation combiner output to carry unit signal input
    route_single(c, cross_section=XS, port1=op_combiner.ports["o3"], port2=carry_unit.ports["signal_in"])

    # =========================
    # 6. MIXER (operation-dependent)
    # =========================
    if operation == 'add':
        mixer = c << sfg_mixer(length=20, name=f"sfg_mixer_{uid}")
        op_label = "ADD_SFG"
    elif operation == 'sub':
        mixer = c << dfg_mixer(length=25, name=f"dfg_mixer_{uid}")
        op_label = "SUB_DFG"
    elif operation == 'mul':
        mixer = c << mul_mixer(length=30, name=f"mul_mixer_{uid}")
        op_label = "MUL_KERR"
    else:
        raise ValueError(f"Unknown operation '{operation}'")

    mixer.dmove((520, -10))

    # Route carry unit to mixer and back
    route_single(c, cross_section=XS, port1=carry_unit.ports["to_mixer"], port2=mixer.ports["input"])
    route_single(c, cross_section=XS, port1=mixer.ports["output"], port2=carry_unit.ports["from_mixer"])

    # =========================
    # 7. OUTPUT STAGE (5 detectors)
    # =========================
    output = c << ternary_output_stage_simple(name=f"output_{uid}", uid=uid)
    output.dmove((700, -10))

    route_single(c, cross_section=XS, port1=carry_unit.ports["to_detectors"], port2=output.ports["input"])

    # =========================
    # 8. LABELS AND PORTS
    # =========================
    c.add_label(f"ALU_OPTICAL_CARRY_{op_label}", position=(400, 100), layer=LABEL_LAYER)
    c.add_label("LASER_IN", position=(-20, 0), layer=LABEL_LAYER)

    # External ports
    c.add_port(name="laser_in", port=frontend.ports["laser_in"])

    # Carry chain ports (connect to adjacent trits)
    c.add_port(name="carry_in_pos", port=carry_unit.ports["carry_in_pos"])
    c.add_port(name="carry_in_neg", port=carry_unit.ports["carry_in_neg"])
    c.add_port(name="carry_out_pos", port=carry_unit.ports["carry_out_pos"])
    c.add_port(name="carry_out_neg", port=carry_unit.ports["carry_out_neg"])

    # Pump laser ports for OPA (external pump sources needed)
    c.add_port(name="pump_in_pos", port=carry_unit.ports["pump_in_pos"])
    c.add_port(name="pump_in_neg", port=carry_unit.ports["pump_in_neg"])
    c.add_port(name="pump_out_pos", port=carry_unit.ports["pump_out_pos"])
    c.add_port(name="pump_out_neg", port=carry_unit.ports["pump_out_neg"])

    return c


def alu_with_wavelength_selectors(
    name: str = "ALU_WithSelectors",
    include_wavelength_selectors: bool = True,
    selector_type: Literal['ring', 'mzi'] = 'mzi'
) -> gf.Component:
    """
    Creates an ALU with integrated input wavelength selectors for each channel.

    This enhanced ALU provides per-channel wavelength gating for precise
    operand selection. Each input (A and B) passes through an AWG demux
    to separate R/G/B wavelengths, then each channel has an independent
    MZI or ring selector for gating, before recombining for the mixer.

    Architecture:
    ```
    Input_A --> AWG(3ch) --> [Sel_R, Sel_G, Sel_B] --> Combiner_A --\\
                                                                     --> universal_alu_mixer() --> AWG(5ch) --> Detectors
    Input_B --> AWG(3ch) --> [Sel_R, Sel_G, Sel_B] --> Combiner_B --/
    ```

    This allows:
    - Individual gating of each wavelength channel per operand
    - Dynamic operand value selection via ctrl_sel_a_r/g/b, ctrl_sel_b_r/g/b
    - Universal ALU operations (add/sub/mul/div) on selected values

    Args:
        name: Component name
        include_wavelength_selectors: If True, adds per-channel selectors.
                                     If False, uses direct AWG->combiner path.
        selector_type: 'ring' for ring resonators, 'mzi' for Mach-Zehnder

    Ports:
        input_a, input_b: Main optical inputs (broadband with R/G/B)
        ctrl_sel_a_r, ctrl_sel_a_g, ctrl_sel_a_b: Selector controls for operand A
        ctrl_sel_b_r, ctrl_sel_b_g, ctrl_sel_b_b: Selector controls for operand B
        ctrl_linear, ctrl_log, ctrl_sfg, ctrl_dfg: ALU operation controls
        out_neg2, out_neg1, out_zero, out_pos1, out_pos2: 5-level output detectors
    """
    import uuid as uuid_mod
    uid = str(uuid_mod.uuid4())[:8]

    c = gf.Component(name)

    # =========================
    # 1. INPUT A - AWG DEMUX + SELECTORS
    # =========================
    awg_a = c << awg_demux(n_channels=3, name=f"awg_a_{uid}")
    awg_a.dmove((0, 50))

    if include_wavelength_selectors:
        # Per-channel selectors for operand A
        if selector_type == 'mzi':
            sel_a_r = c << wavelength_selector_mzi(wavelength_um=1.550, name=f"sel_a_r_{uid}")
            sel_a_g = c << wavelength_selector_mzi(wavelength_um=1.216, name=f"sel_a_g_{uid}")
            sel_a_b = c << wavelength_selector_mzi(wavelength_um=1.000, name=f"sel_a_b_{uid}")
        else:
            sel_a_r = c << wavelength_selector(wavelength_um=1.550, name=f"sel_a_r_{uid}")
            sel_a_g = c << wavelength_selector(wavelength_um=1.216, name=f"sel_a_g_{uid}")
            sel_a_b = c << wavelength_selector(wavelength_um=1.000, name=f"sel_a_b_{uid}")

        sel_a_r.dmove((80, 70))
        sel_a_g.dmove((80, 50))
        sel_a_b.dmove((80, 30))

        # Route AWG outputs to selectors
        route_single(c, cross_section=XS, port1=awg_a.ports["out_r"], port2=sel_a_r.ports["input"])
        route_single(c, cross_section=XS, port1=awg_a.ports["out_g"], port2=sel_a_g.ports["input"])
        route_single(c, cross_section=XS, port1=awg_a.ports["out_b"], port2=sel_a_b.ports["input"])

        # Combiner for A (after selectors)
        comb_a = c << wavelength_combiner(n_inputs=3, name=f"comb_a_{uid}")
        comb_a.dmove((180, 50))

        route_single(c, cross_section=XS, port1=sel_a_r.ports["output"], port2=comb_a.ports["in1"])
        route_single(c, cross_section=XS, port1=sel_a_g.ports["output"], port2=comb_a.ports["in2"])
        route_single(c, cross_section=XS, port1=sel_a_b.ports["output"], port2=comb_a.ports["in3"])
    else:
        # Direct path without selectors
        comb_a = c << wavelength_combiner(n_inputs=3, name=f"comb_a_{uid}")
        comb_a.dmove((100, 50))

        route_single(c, cross_section=XS, port1=awg_a.ports["out_r"], port2=comb_a.ports["in1"])
        route_single(c, cross_section=XS, port1=awg_a.ports["out_g"], port2=comb_a.ports["in2"])
        route_single(c, cross_section=XS, port1=awg_a.ports["out_b"], port2=comb_a.ports["in3"])

    # =========================
    # 2. INPUT B - AWG DEMUX + SELECTORS
    # =========================
    awg_b = c << awg_demux(n_channels=3, name=f"awg_b_{uid}")
    awg_b.dmove((0, -50))

    if include_wavelength_selectors:
        # Per-channel selectors for operand B
        if selector_type == 'mzi':
            sel_b_r = c << wavelength_selector_mzi(wavelength_um=1.550, name=f"sel_b_r_{uid}")
            sel_b_g = c << wavelength_selector_mzi(wavelength_um=1.216, name=f"sel_b_g_{uid}")
            sel_b_b = c << wavelength_selector_mzi(wavelength_um=1.000, name=f"sel_b_b_{uid}")
        else:
            sel_b_r = c << wavelength_selector(wavelength_um=1.550, name=f"sel_b_r_{uid}")
            sel_b_g = c << wavelength_selector(wavelength_um=1.216, name=f"sel_b_g_{uid}")
            sel_b_b = c << wavelength_selector(wavelength_um=1.000, name=f"sel_b_b_{uid}")

        sel_b_r.dmove((80, -30))
        sel_b_g.dmove((80, -50))
        sel_b_b.dmove((80, -70))

        # Route AWG outputs to selectors
        route_single(c, cross_section=XS, port1=awg_b.ports["out_r"], port2=sel_b_r.ports["input"])
        route_single(c, cross_section=XS, port1=awg_b.ports["out_g"], port2=sel_b_g.ports["input"])
        route_single(c, cross_section=XS, port1=awg_b.ports["out_b"], port2=sel_b_b.ports["input"])

        # Combiner for B (after selectors)
        comb_b = c << wavelength_combiner(n_inputs=3, name=f"comb_b_{uid}")
        comb_b.dmove((180, -50))

        route_single(c, cross_section=XS, port1=sel_b_r.ports["output"], port2=comb_b.ports["in1"])
        route_single(c, cross_section=XS, port1=sel_b_g.ports["output"], port2=comb_b.ports["in2"])
        route_single(c, cross_section=XS, port1=sel_b_b.ports["output"], port2=comb_b.ports["in3"])
    else:
        # Direct path without selectors
        comb_b = c << wavelength_combiner(n_inputs=3, name=f"comb_b_{uid}")
        comb_b.dmove((100, -50))

        route_single(c, cross_section=XS, port1=awg_b.ports["out_r"], port2=comb_b.ports["in1"])
        route_single(c, cross_section=XS, port1=awg_b.ports["out_g"], port2=comb_b.ports["in2"])
        route_single(c, cross_section=XS, port1=awg_b.ports["out_b"], port2=comb_b.ports["in3"])

    # =========================
    # 3. COMBINE A + B INTO UNIVERSAL ALU MIXER
    # =========================
    # Pre-mixer combiner
    pre_mixer = c << gf.components.mmi2x2()
    pre_mixer.dmove((250, 0))

    route_single(c, cross_section=XS, port1=comb_a.ports["output"], port2=pre_mixer.ports["o1"])
    route_single(c, cross_section=XS, port1=comb_b.ports["output"], port2=pre_mixer.ports["o2"])

    # Universal ALU Mixer (add/sub/mul/div)
    alu = c << universal_alu_mixer(name=f"alu_{uid}", uid=uid)
    alu.dmove((300, 0))

    route_single(c, cross_section=XS, port1=pre_mixer.ports["o3"], port2=alu.ports["input"])

    # =========================
    # 4. OUTPUT STAGE - 5-CHANNEL AWG + DETECTORS
    # =========================
    awg_out = c << awg_demux(n_channels=5, name=f"awg_out_{uid}")
    awg_out.dmove((770, 0))

    route_single(c, cross_section=XS, port1=alu.ports["output"], port2=awg_out.ports["input"])

    # 5 photodetectors for output values
    det_neg2 = c << photodetector(name=f"det_neg2_{uid}")
    det_neg1 = c << photodetector(name=f"det_neg1_{uid}")
    det_zero = c << photodetector(name=f"det_zero_{uid}")
    det_pos1 = c << photodetector(name=f"det_pos1_{uid}")
    det_pos2 = c << photodetector(name=f"det_pos2_{uid}")

    det_neg2.dmove((870, 30))
    det_neg1.dmove((870, 15))
    det_zero.dmove((870, 0))
    det_pos1.dmove((870, -15))
    det_pos2.dmove((870, -30))

    route_single(c, cross_section=XS, port1=awg_out.ports["out_1"], port2=det_neg2.ports["input"])
    route_single(c, cross_section=XS, port1=awg_out.ports["out_2"], port2=det_neg1.ports["input"])
    route_single(c, cross_section=XS, port1=awg_out.ports["out_3"], port2=det_zero.ports["input"])
    route_single(c, cross_section=XS, port1=awg_out.ports["out_4"], port2=det_pos1.ports["input"])
    route_single(c, cross_section=XS, port1=awg_out.ports["out_5"], port2=det_pos2.ports["input"])

    # =========================
    # 5. LABELS
    # =========================
    c.add_label("ALU_WITH_WAVELENGTH_SELECTORS", position=(400, 100), layer=LABEL_LAYER)
    c.add_label("INPUT_A", position=(-30, 50), layer=LABEL_LAYER)
    c.add_label("INPUT_B", position=(-30, -50), layer=LABEL_LAYER)
    c.add_label("AWG_3ch", position=(20, 65), layer=LABEL_LAYER)
    c.add_label("AWG_3ch", position=(20, -35), layer=LABEL_LAYER)
    c.add_label("AWG_5ch", position=(790, 40), layer=LABEL_LAYER)

    if include_wavelength_selectors:
        c.add_label("SEL_R", position=(100, 75), layer=LABEL_LAYER)
        c.add_label("SEL_G", position=(100, 55), layer=LABEL_LAYER)
        c.add_label("SEL_B", position=(100, 35), layer=LABEL_LAYER)
        c.add_label("SEL_R", position=(100, -25), layer=LABEL_LAYER)
        c.add_label("SEL_G", position=(100, -45), layer=LABEL_LAYER)
        c.add_label("SEL_B", position=(100, -65), layer=LABEL_LAYER)

    c.add_label("DET_-2 (0.775um)", position=(890, 30), layer=LABEL_LAYER)
    c.add_label("DET_-1 (0.681um)", position=(890, 15), layer=LABEL_LAYER)
    c.add_label("DET_0 (0.608um)", position=(890, 0), layer=LABEL_LAYER)
    c.add_label("DET_+1 (0.549um)", position=(890, -15), layer=LABEL_LAYER)
    c.add_label("DET_+2 (0.500um)", position=(890, -30), layer=LABEL_LAYER)

    # =========================
    # 6. PORTS
    # =========================
    # Main inputs
    c.add_port(name="input_a", port=awg_a.ports["input"])
    c.add_port(name="input_b", port=awg_b.ports["input"])

    # Selector control ports (if selectors are included)
    if include_wavelength_selectors:
        # Note: These are virtual ports for documentation - actual control
        # is via the heater electrodes on the MZI/ring selectors
        pad_w = 10
        c.add_port(name="ctrl_sel_a_r", center=(95, 85), width=pad_w, orientation=90, layer=HEATER_LAYER)
        c.add_port(name="ctrl_sel_a_g", center=(95, 60), width=pad_w, orientation=90, layer=HEATER_LAYER)
        c.add_port(name="ctrl_sel_a_b", center=(95, 40), width=pad_w, orientation=90, layer=HEATER_LAYER)
        c.add_port(name="ctrl_sel_b_r", center=(95, -20), width=pad_w, orientation=90, layer=HEATER_LAYER)
        c.add_port(name="ctrl_sel_b_g", center=(95, -45), width=pad_w, orientation=90, layer=HEATER_LAYER)
        c.add_port(name="ctrl_sel_b_b", center=(95, -60), width=pad_w, orientation=90, layer=HEATER_LAYER)

    # ALU operation controls (from universal_alu_mixer)
    c.add_port(name="ctrl_linear", port=alu.ports["ctrl_linear"])
    c.add_port(name="ctrl_log", port=alu.ports["ctrl_log"])
    c.add_port(name="ctrl_sfg", port=alu.ports["ctrl_sfg"])
    c.add_port(name="ctrl_dfg", port=alu.ports["ctrl_dfg"])
    c.add_port(name="pump_exp", port=alu.ports["pump_exp"])

    # Output detector ports (electrical pads - detectors convert optical to electrical)
    # Use detector input positions as reference for electrical output pads
    det_pad_layer = (12, 0)  # Metal pad layer
    c.add_port(name="out_neg2", center=(890, 30), width=10, orientation=0, layer=det_pad_layer)
    c.add_port(name="out_neg1", center=(890, 15), width=10, orientation=0, layer=det_pad_layer)
    c.add_port(name="out_zero", center=(890, 0), width=10, orientation=0, layer=det_pad_layer)
    c.add_port(name="out_pos1", center=(890, -15), width=10, orientation=0, layer=det_pad_layer)
    c.add_port(name="out_pos2", center=(890, -30), width=10, orientation=0, layer=det_pad_layer)

    return c


def generate_81_trit_processor(
    name: str = "Ternary81"
) -> gf.Component:
    """
    Generates the optimal 81-trit (3^4) ternary processor.

    Architecture:
      - 81 trits = 128-bit equivalent
      - Organized as 9×9 grid of nonads (9-trit units)
      - Each nonad contains 3 trytes (3-trit units)
      - Hierarchical: 81 = 3 × 27 = 9 × 9 = 27 × 3

    Layout:
      +---------------------------+
      | Nonad | Nonad | Nonad |   Row 0 (trits 0-26)
      | 0-8   | 9-17  | 18-26 |
      +---------------------------+
      | Nonad | Nonad | Nonad |   Row 1 (trits 27-53)
      | 27-35 | 36-44 | 45-53 |
      +---------------------------+
      | Nonad | Nonad | Nonad |   Row 2 (trits 54-80)
      | 54-62 | 63-71 | 72-80 |
      +---------------------------+
    """
    import uuid
    c = gf.Component(name)

    # 81-trit processor organized as 3x3 grid of 27-trit "heptacosas"
    # Each heptacosa contains 3x3 = 9 trytes
    # Each tryte contains 3 trits

    x_spacing = 400  # Horizontal spacing between columns
    y_spacing = 200  # Vertical spacing between rows

    trit_index = 0

    # Create 3 rows of 3 heptacosas (27 trits each)
    for row in range(3):  # 3 heptacosas vertically
        for col in range(3):  # 3 nonads per heptacosa horizontally
            for sub in range(3):  # 3 trytes per nonad
                for trit in range(3):  # 3 trits per tryte
                    uid = str(uuid.uuid4())[:8]
                    alu = c << generate_ternary_alu(
                        operations=["add", "subtract", "multiply", "divide"],
                        name=f"ALU_t{trit_index}_{uid}"
                    )

                    # Position: spread across grid
                    x_pos = col * x_spacing + sub * 120
                    y_pos = row * (y_spacing * 9) + trit * y_spacing

                    alu.dmove((x_pos, y_pos))
                    trit_index += 1

    # Add hierarchical labels
    c.add_label("CPU_81T", position=(600, -100), layer=LABEL_LAYER)

    # Label the three 27-trit sections
    for row in range(3):
        y_label = row * (y_spacing * 9) + y_spacing * 4
        c.add_label(f"H{row}", position=(-100, y_label), layer=LABEL_LAYER)

    return c


def cascaded_splitter_1to9(
    name: str = "split_1to9",
    uid: str = ""
) -> gf.Component:
    """
    Creates a 1-to-9 splitter tree using cascaded 1x3 stages.

    Structure: 1 → 3 → 9
    """
    import uuid
    if not uid:
        uid = str(uuid.uuid4())[:8]

    c = gf.Component(name)

    # First stage: 1 to 3
    split1 = c << wavelength_splitter(n_outputs=3, name=f"s1_{uid}")
    split1.dmove((0, 0))

    # Second stage: 3 splitters, each 1 to 3
    outputs = []
    for i in range(3):
        split2 = c << wavelength_splitter(n_outputs=3, name=f"s2_{i}_{uid}")
        y_offset = (i - 1) * 80
        split2.dmove((80, y_offset))

        # Route from first stage
        route_single(c, cross_section=XS,
                    port1=split1.ports[f"out{i+1}"],
                    port2=split2.ports["input"])

        # Collect output ports
        for j in range(3):
            outputs.append((split2, f"out{j+1}", i * 3 + j))

    # Input port
    c.add_port(name="input", port=split1.ports["input"])

    # Output ports (9 total)
    for split2, port_name, idx in outputs:
        c.add_port(name=f"out{idx}", port=split2.ports[port_name])

    return c
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
